andraz213/UrbanNoiseSensing/Diplomska naloga/fotografije/ekran_gateway.jpg

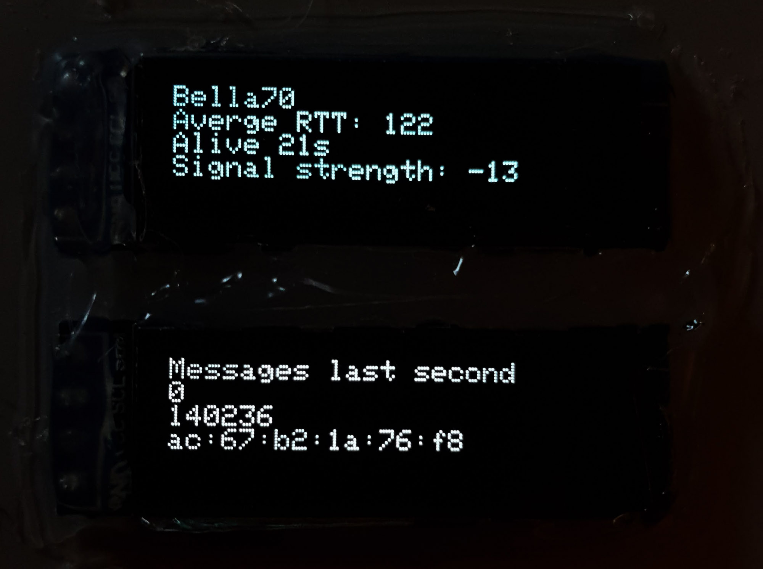
Diplomska naloga/fotografije/ekran_gateway.jpg
