andraz213/UrbanNoiseSensing/Diplomska naloga/fotografije/nastavljanje.jpg

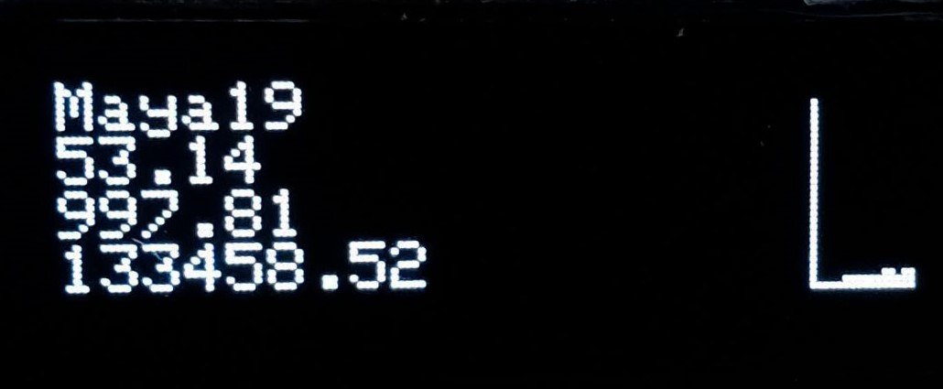
Diplomska naloga/fotografije/nastavljanje.jpg
