andraz213/UrbanNoiseSensing/Diplomska naloga/fotografije/nastavljanje_nastavljenno.jpg

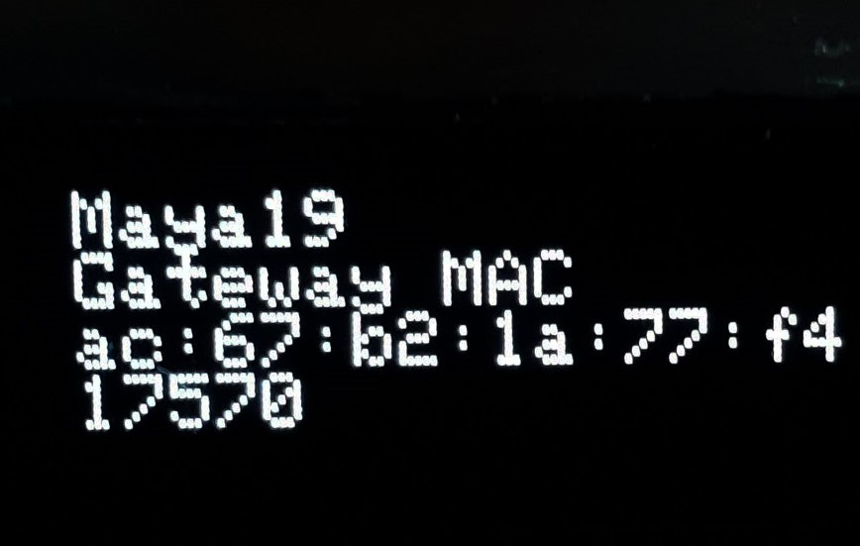
Diplomska naloga/fotografije/nastavljanje_nastavljenno.jpg
