andraz213/UrbanNoiseSensing/Diplomska naloga/fotografije/nastavljeno_nenastavljeno.jpg

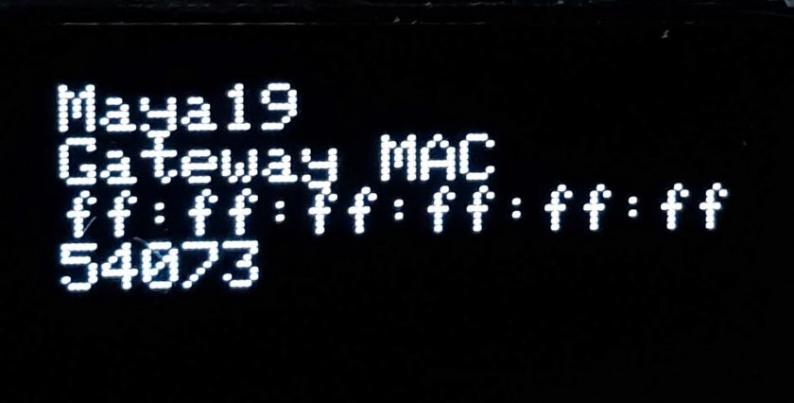
Diplomska naloga/fotografije/nastavljeno_nenastavljeno.jpg
