andraz213/UrbanNoiseSensing/Diplomska naloga/fotografije/polnenje.jpg

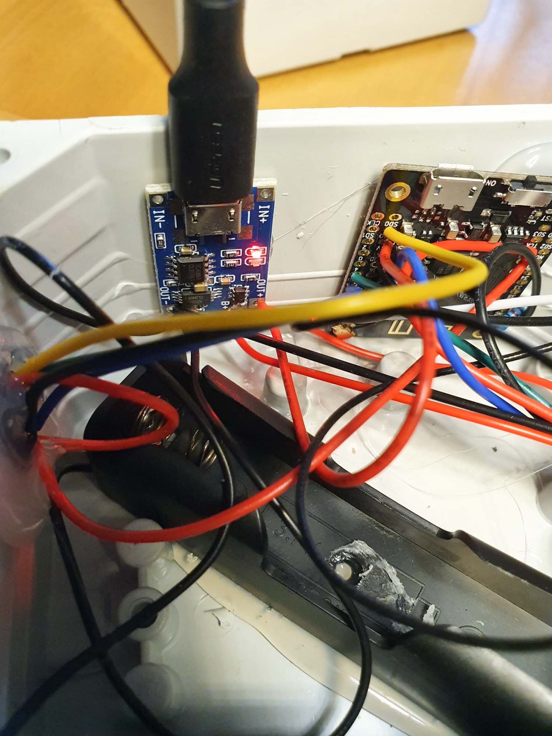
Diplomska naloga/fotografije/polnenje.jpg
