andraz213/UrbanNoiseSensing/Diplomska naloga/fotografije/polnenje_done.jpg

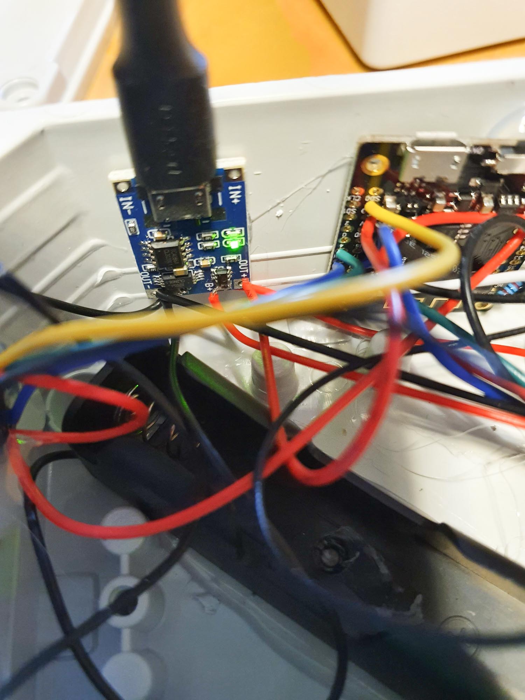
Diplomska naloga/fotografije/polnenje_done.jpg
