andraz213/UrbanNoiseSensing/Diplomska naloga/fotografije/priziganje_zaznavanje.jpg

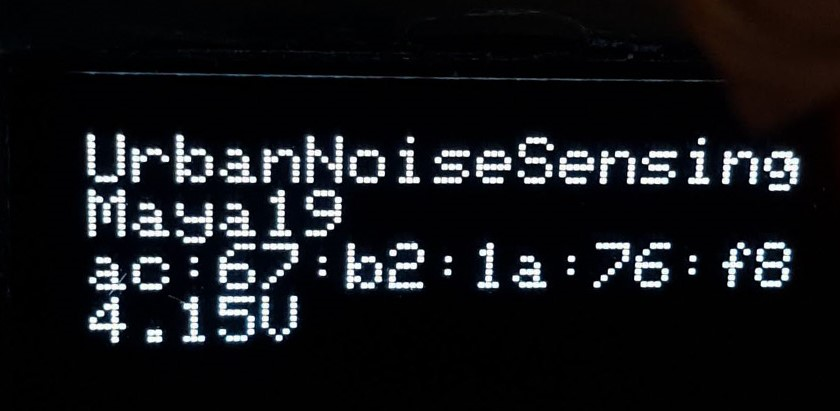
Diplomska naloga/fotografije/priziganje_zaznavanje.jpg
