andraz213/UrbanNoiseSensing/Diplomska naloga/fotografije/sestavljena_merilna1.jpg

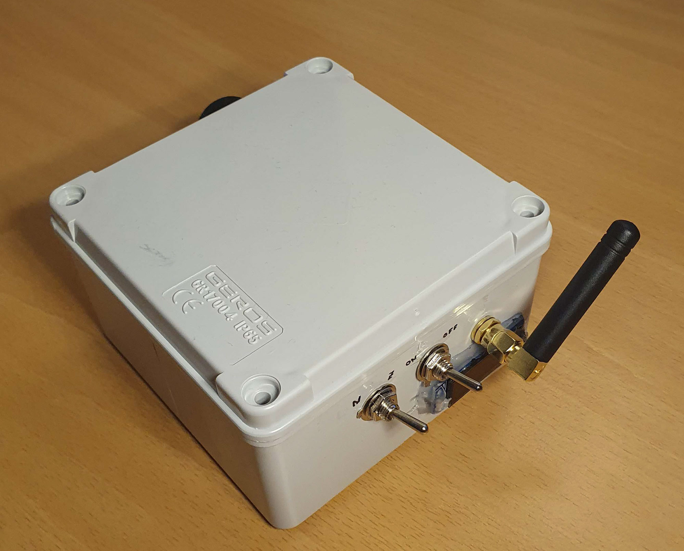
Diplomska naloga/fotografije/sestavljena_merilna1.jpg
