andraz213/UrbanNoiseSensing/Diplomska naloga/fotografije/sestavljena_merilna3.jpg

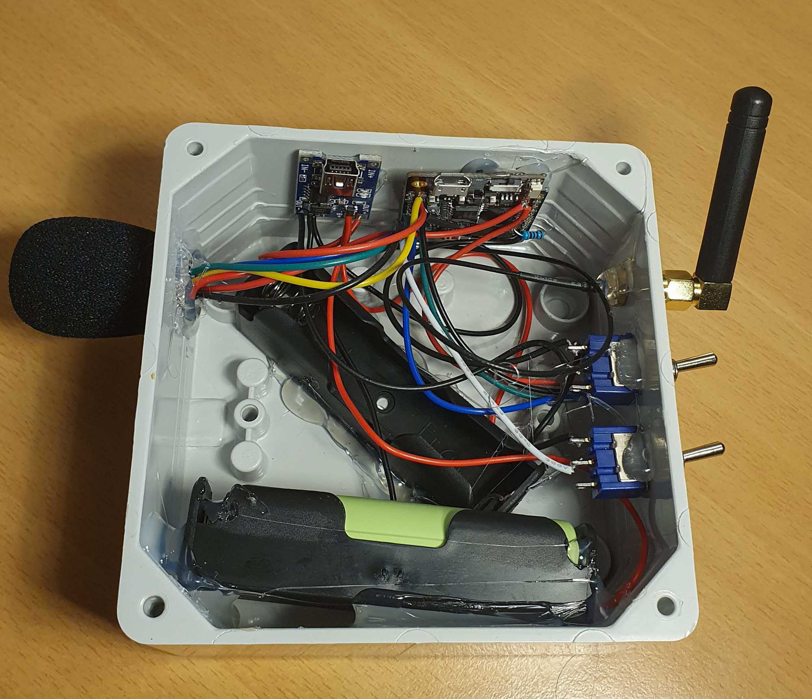
Diplomska naloga/fotografije/sestavljena_merilna3.jpg
