andraz213/UrbanNoiseSensing/Diplomska naloga/fotografije/sestavljena_zbirna1.jpg

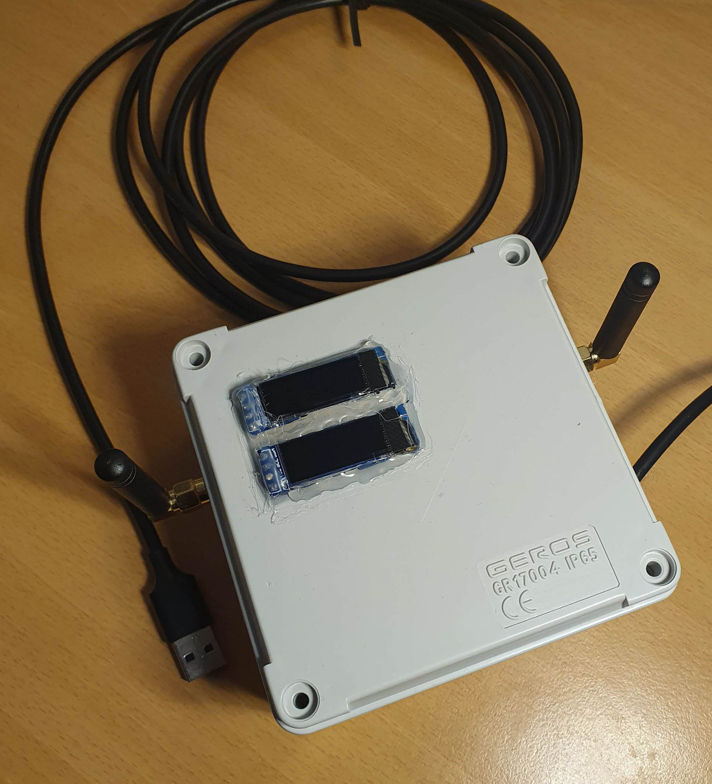
Diplomska naloga/fotografije/sestavljena_zbirna1.jpg
