andraz213/UrbanNoiseSensing/Diplomska naloga/fotografije/sestavljena_zbirna2.jpg

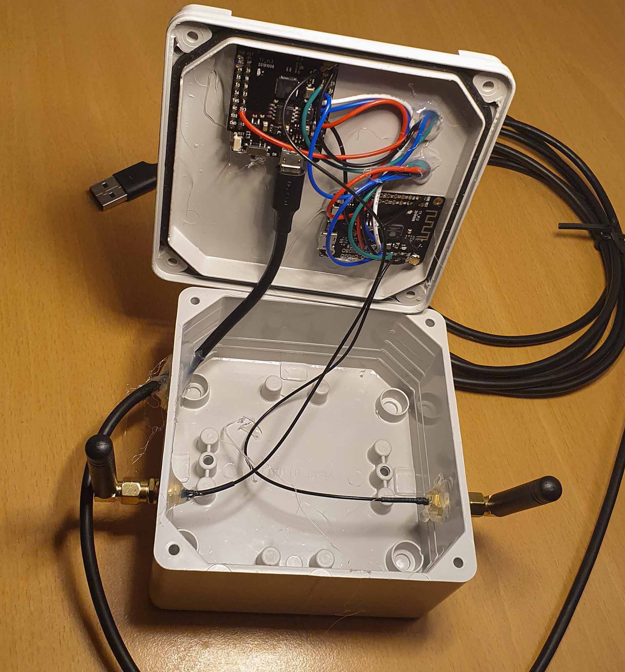
Diplomska naloga/fotografije/sestavljena_zbirna2.jpg
