andraz213/UrbanNoiseSensing/Diplomska naloga/fotografije/stikala.jpg

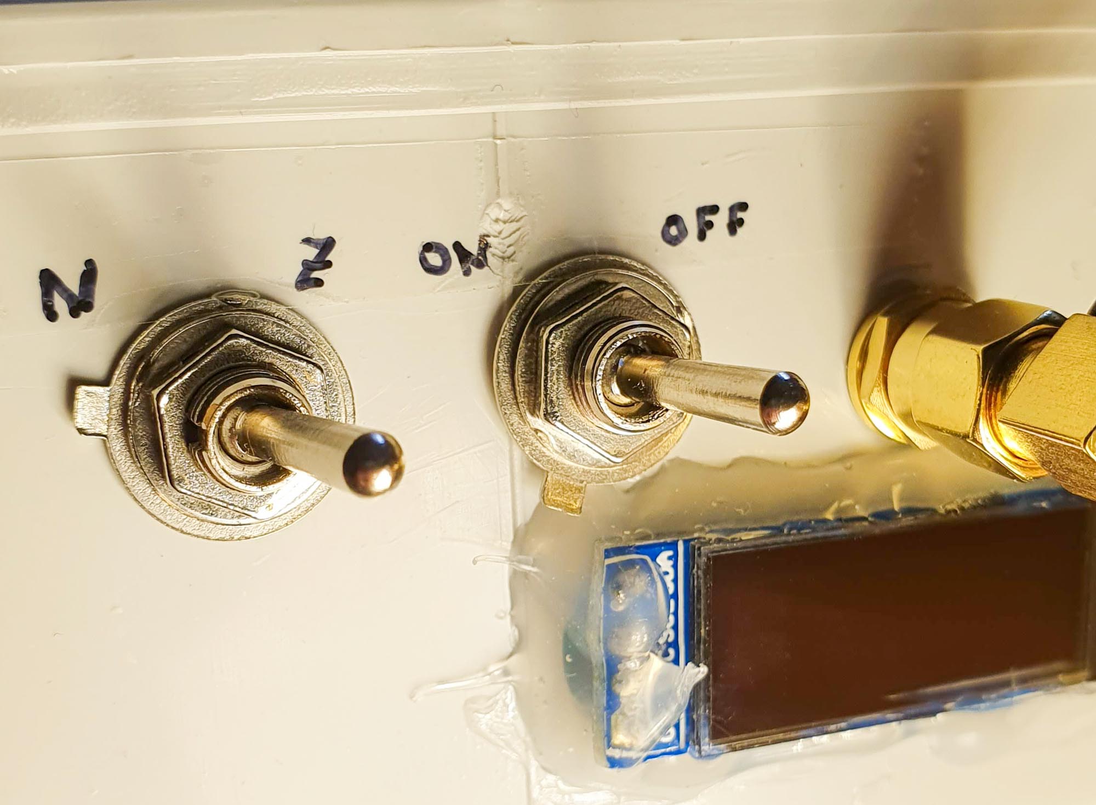
Diplomska naloga/fotografije/stikala.jpg
