andraz213/UrbanNoiseSensing/Diplomska naloga/slike/data_matrica.png

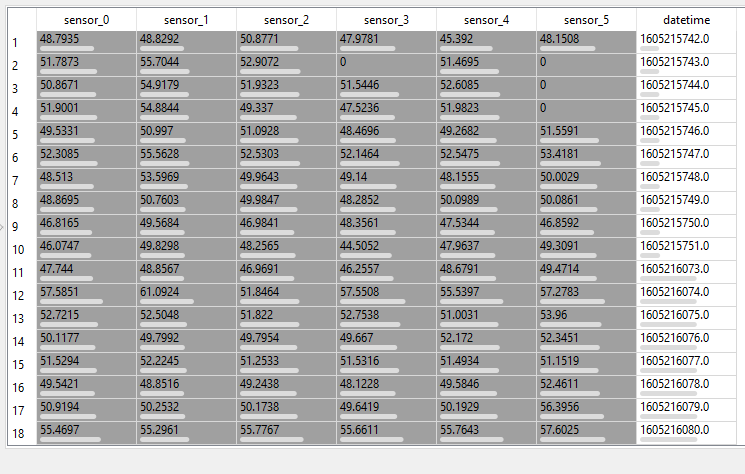
Diplomska naloga/slike/data_matrica.png
