andraz213/UrbanNoiseSensing/Diplomska naloga/slike/data_tenzorji.png

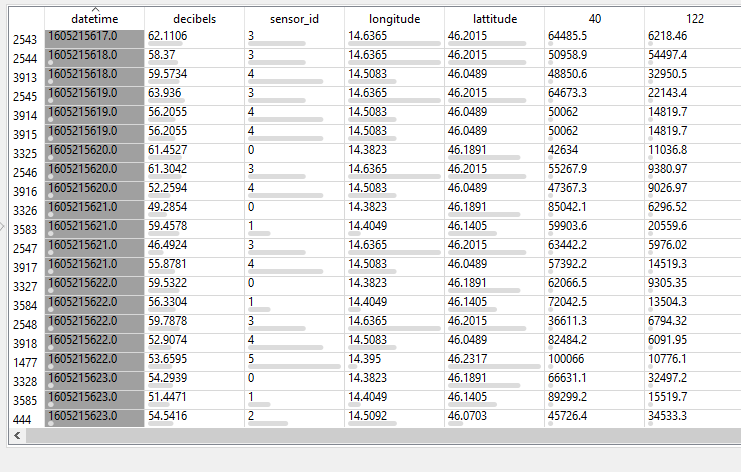
Diplomska naloga/slike/data_tenzorji.png
