andraz213/UrbanNoiseSensing/Diplomska naloga/slike/db_data.jpg

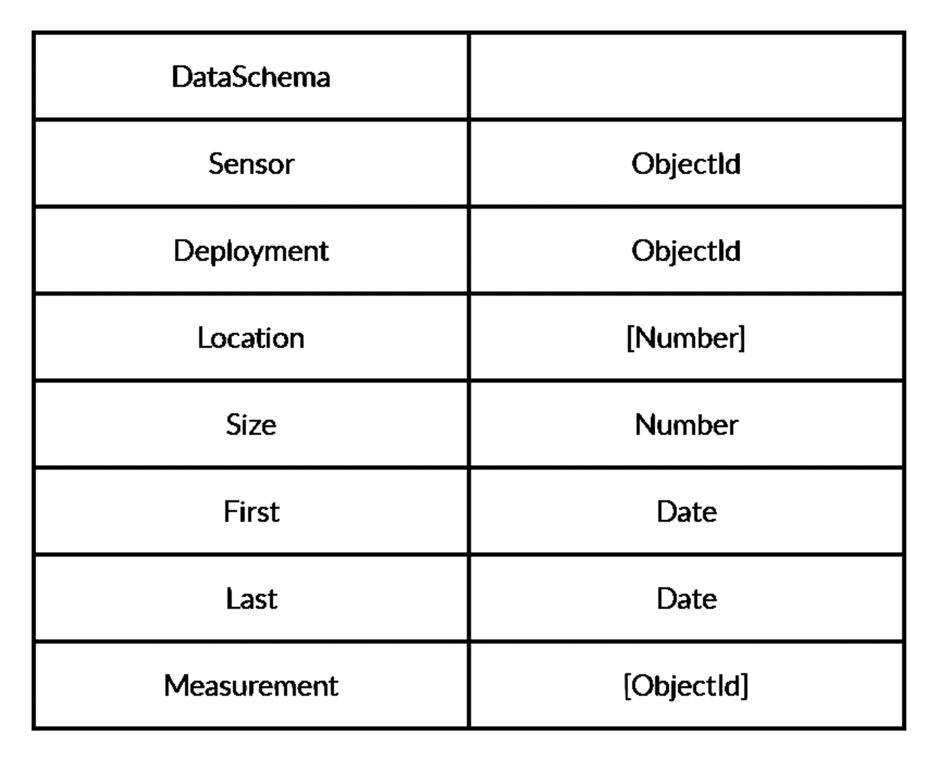
Diplomska naloga/slike/db_data.jpg
