andraz213/UrbanNoiseSensing/Diplomska naloga/slike/db_deployment.jpg

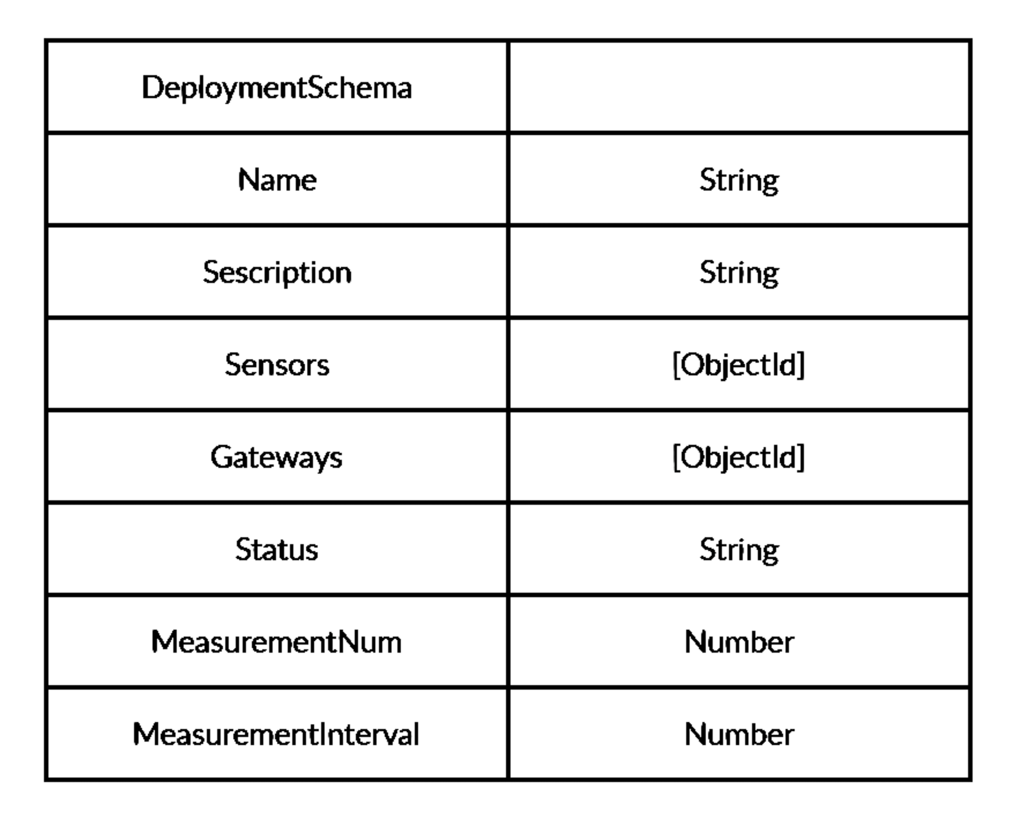
Diplomska naloga/slike/db_deployment.jpg
