andraz213/UrbanNoiseSensing/Diplomska naloga/slike/db_merilna_zbirna.jpg

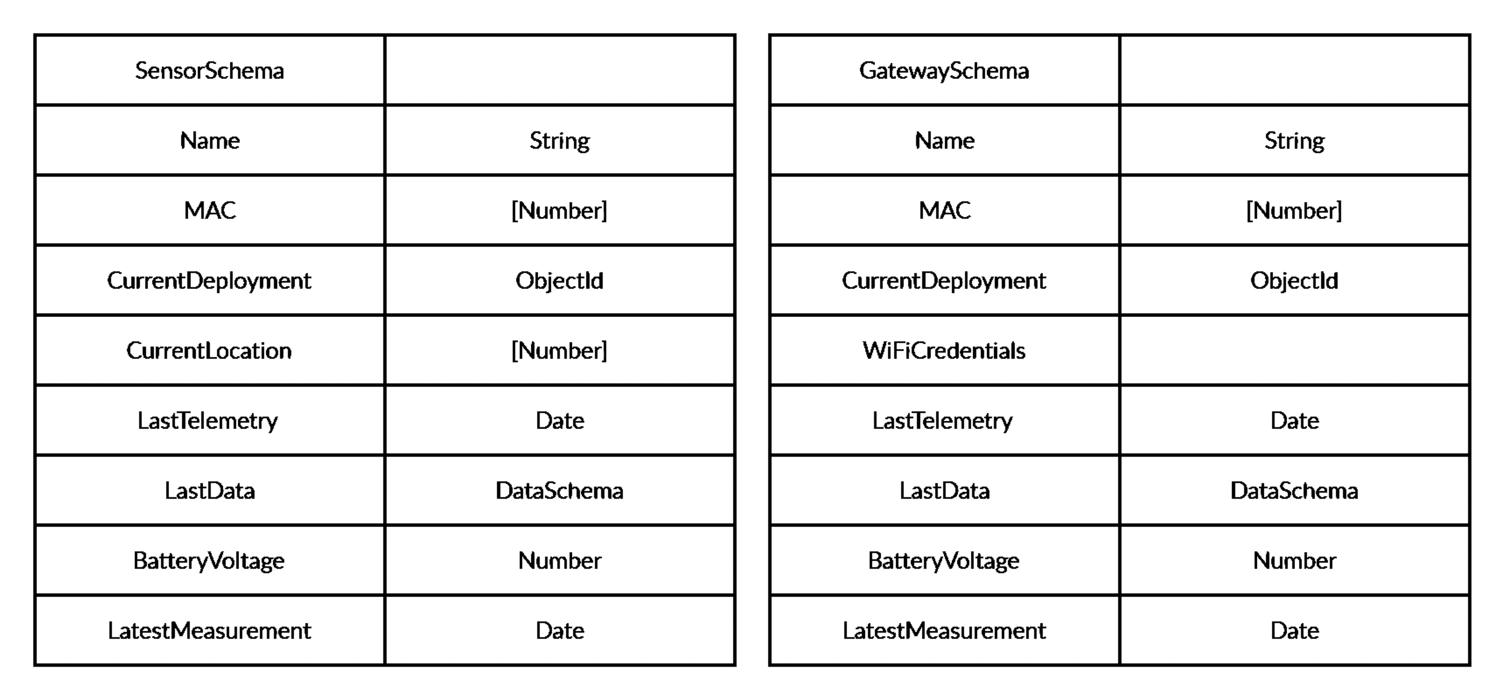
Diplomska naloga/slike/db_merilna_zbirna.jpg
