andraz213/UrbanNoiseSensing/Diplomska naloga/slike/Detajli poraba.png

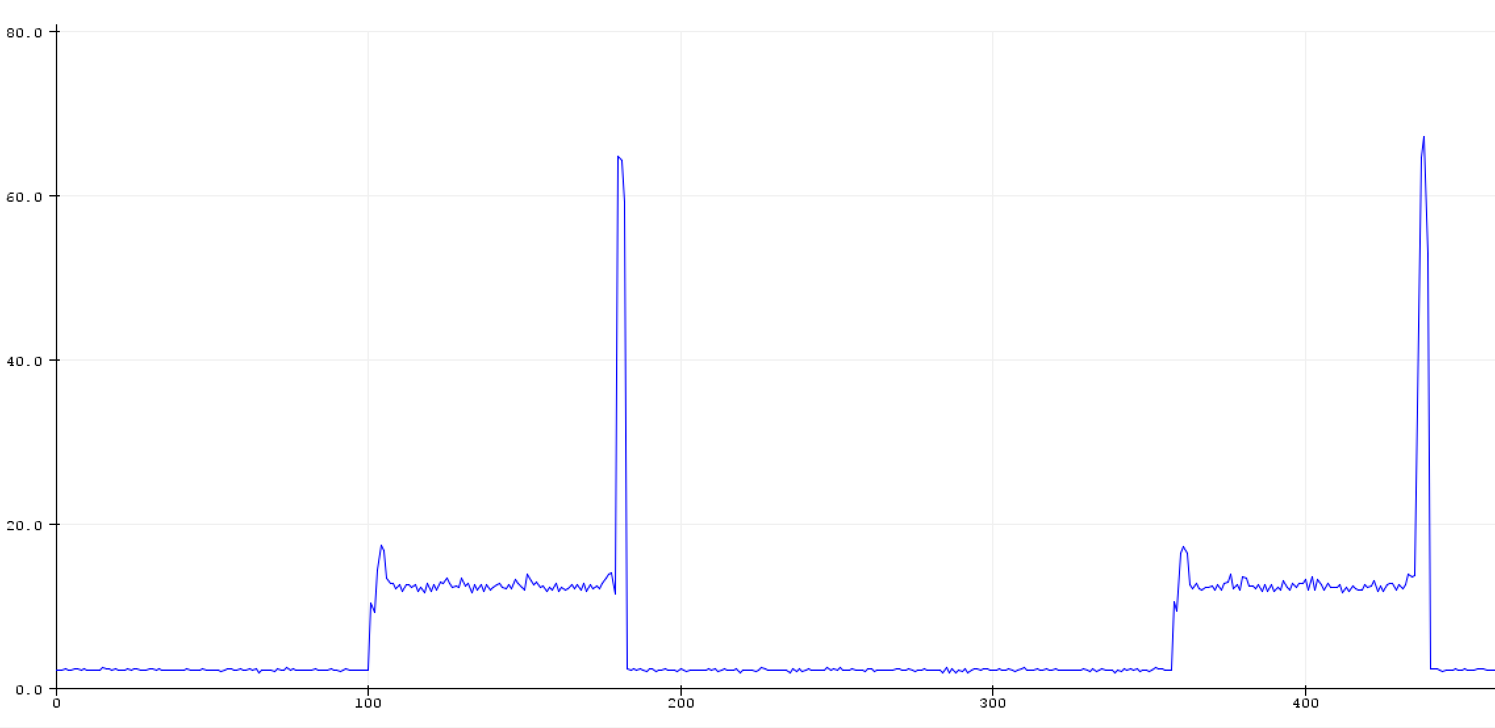
Diplomska naloga/slike/Detajli poraba.png
