andraz213/UrbanNoiseSensing/Diplomska naloga/slike/graf_dnevi_dnevna.png

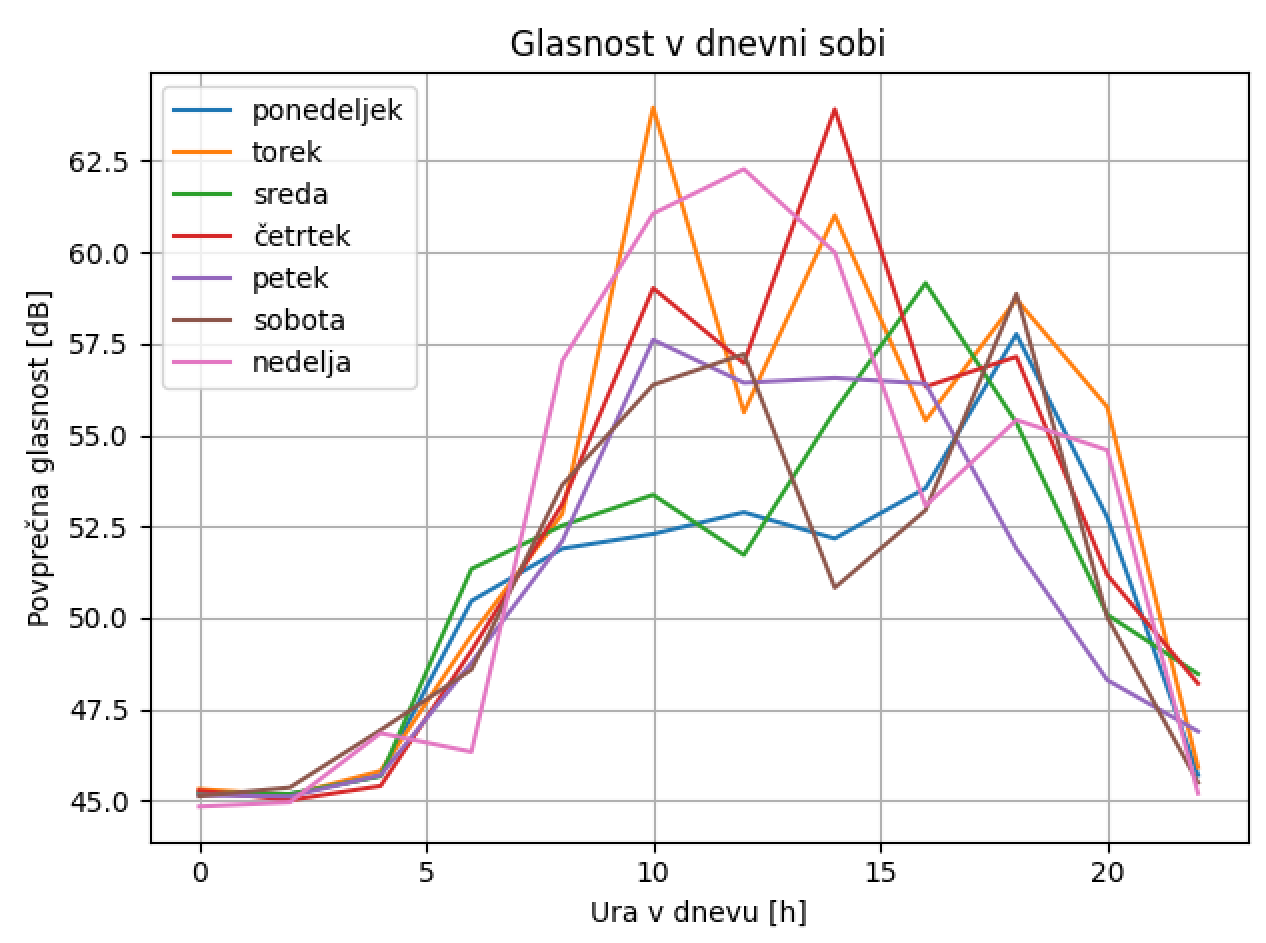
Diplomska naloga/slike/graf_dnevi_dnevna.png
