andraz213/UrbanNoiseSensing/Diplomska naloga/slike/graf_dnevna.png

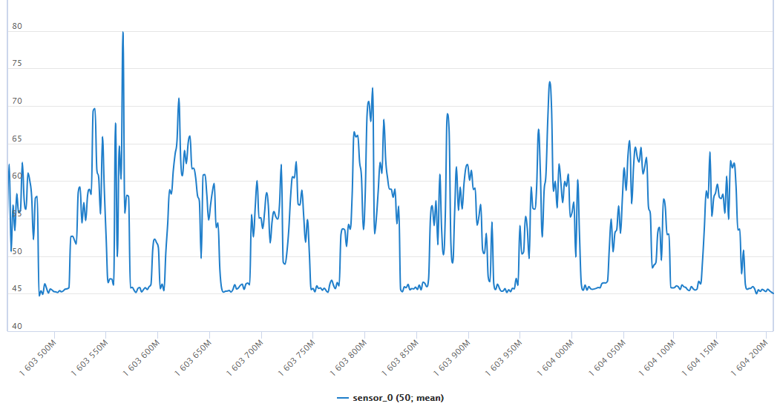
Diplomska naloga/slike/graf_dnevna.png
