andraz213/UrbanNoiseSensing/Diplomska naloga/slike/Konceptualna shema merilne enote (2)_popravljeno.jpg

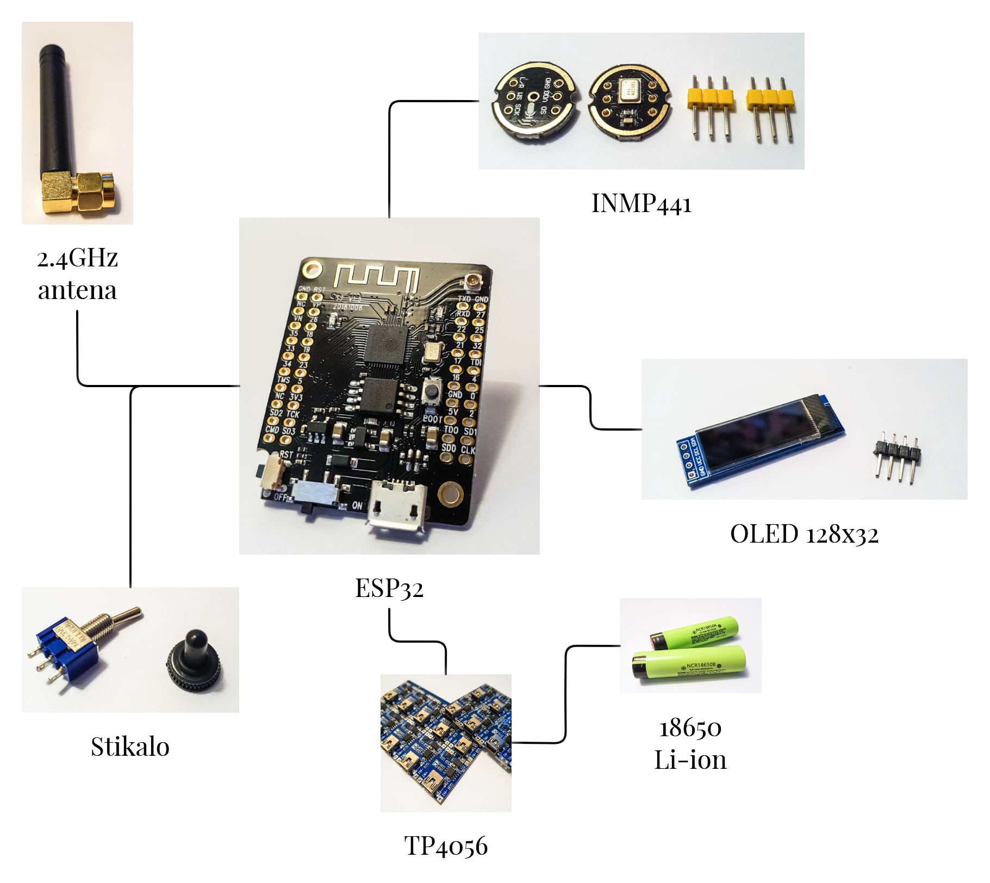
Diplomska naloga/slike/Konceptualna shema merilne enote (2)_popravljeno.jpg
