andraz213/UrbanNoiseSensing/Diplomska naloga/slike/kosilnica mapa 2.png

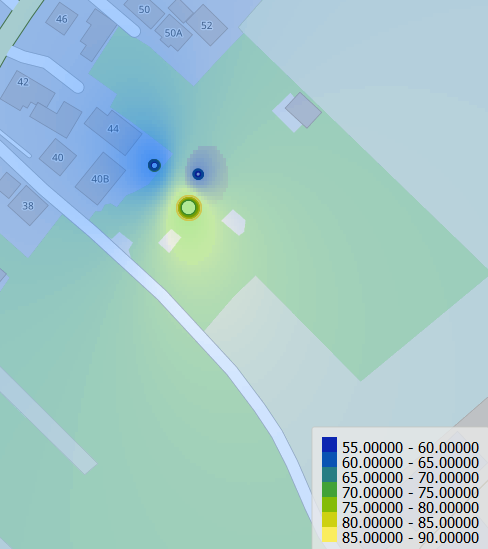
Diplomska naloga/slike/kosilnica mapa 2.png
