andraz213/UrbanNoiseSensing/Diplomska naloga/slike/Kosilnica mapa.png

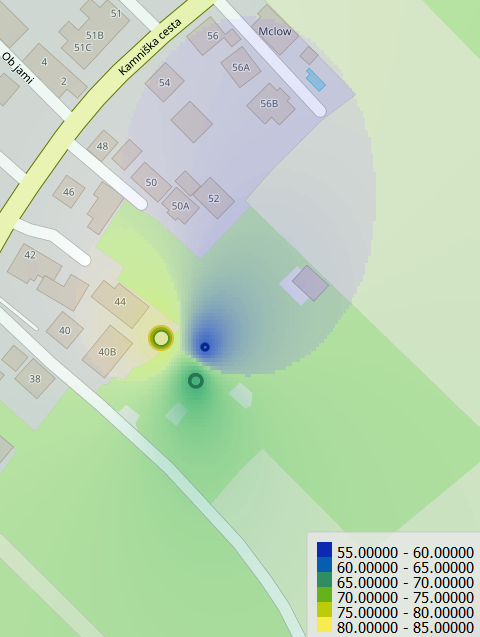
Diplomska naloga/slike/Kosilnica mapa.png
