andraz213/UrbanNoiseSensing/Diplomska naloga/slike/kosilnica_graf.png

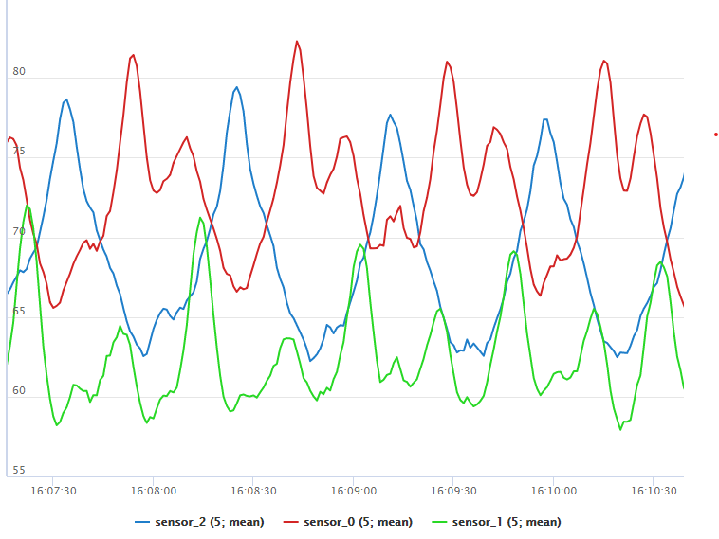
Diplomska naloga/slike/kosilnica_graf.png
