andraz213/UrbanNoiseSensing/Diplomska naloga/slike/Libellium_enote.png

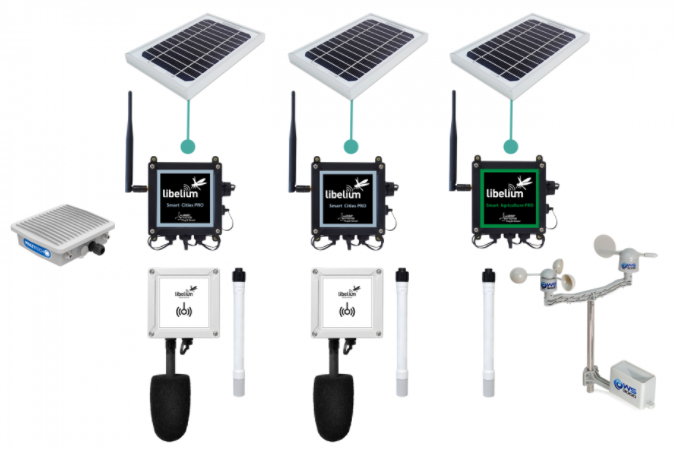
Diplomska naloga/slike/Libellium_enote.png
