andraz213/UrbanNoiseSensing/Diplomska naloga/slike/Merilna enota delovanje (1)_popravljeno.jpg

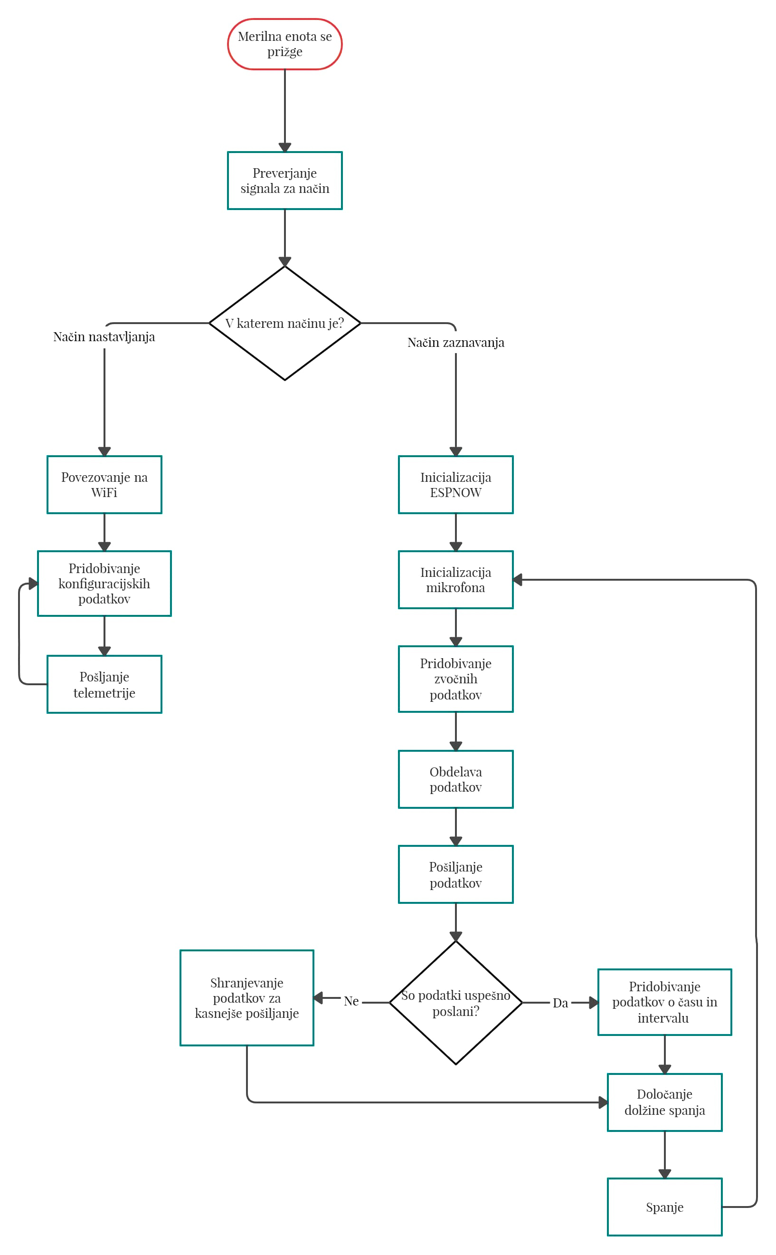
Diplomska naloga/slike/Merilna enota delovanje (1)_popravljeno.jpg
