andraz213/UrbanNoiseSensing/Diplomska naloga/slike/Normalna poraba na eno sekundo.png

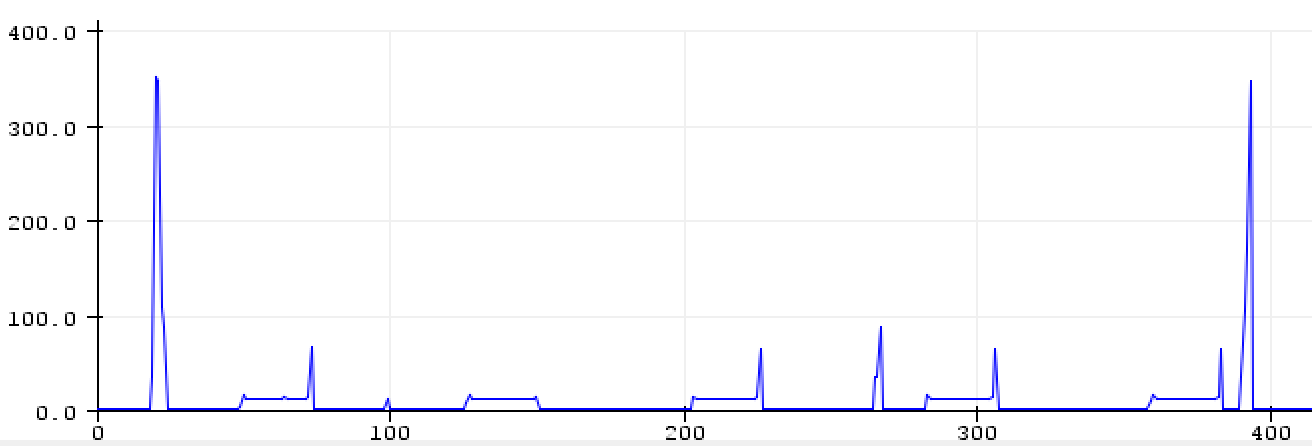
Diplomska naloga/slike/Normalna poraba na eno sekundo.png
