andraz213/UrbanNoiseSensing/Diplomska naloga/slike/periodogram_dnnevna.png

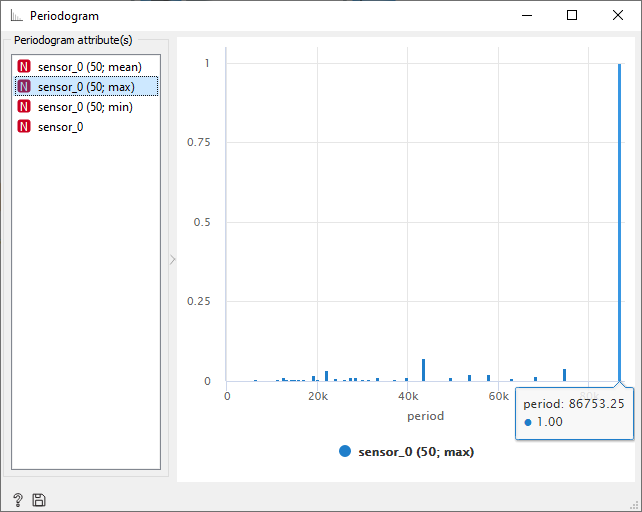
Diplomska naloga/slike/periodogram_dnnevna.png
