andraz213/UrbanNoiseSensing/Diplomska naloga/slike/podoben_mojemu.png

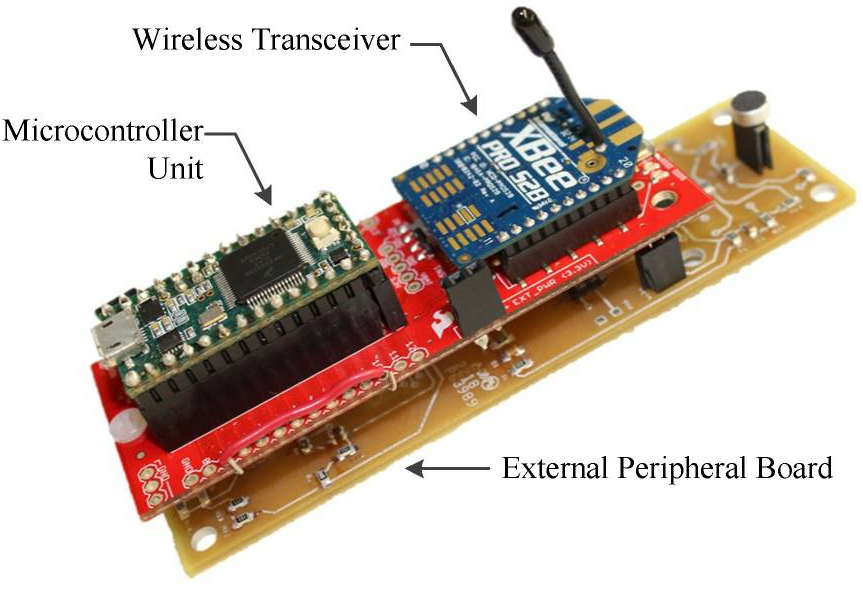
Diplomska naloga/slike/podoben_mojemu.png
