andraz213/UrbanNoiseSensing/Diplomska naloga/slike/poraba_detaili_fakpng.png

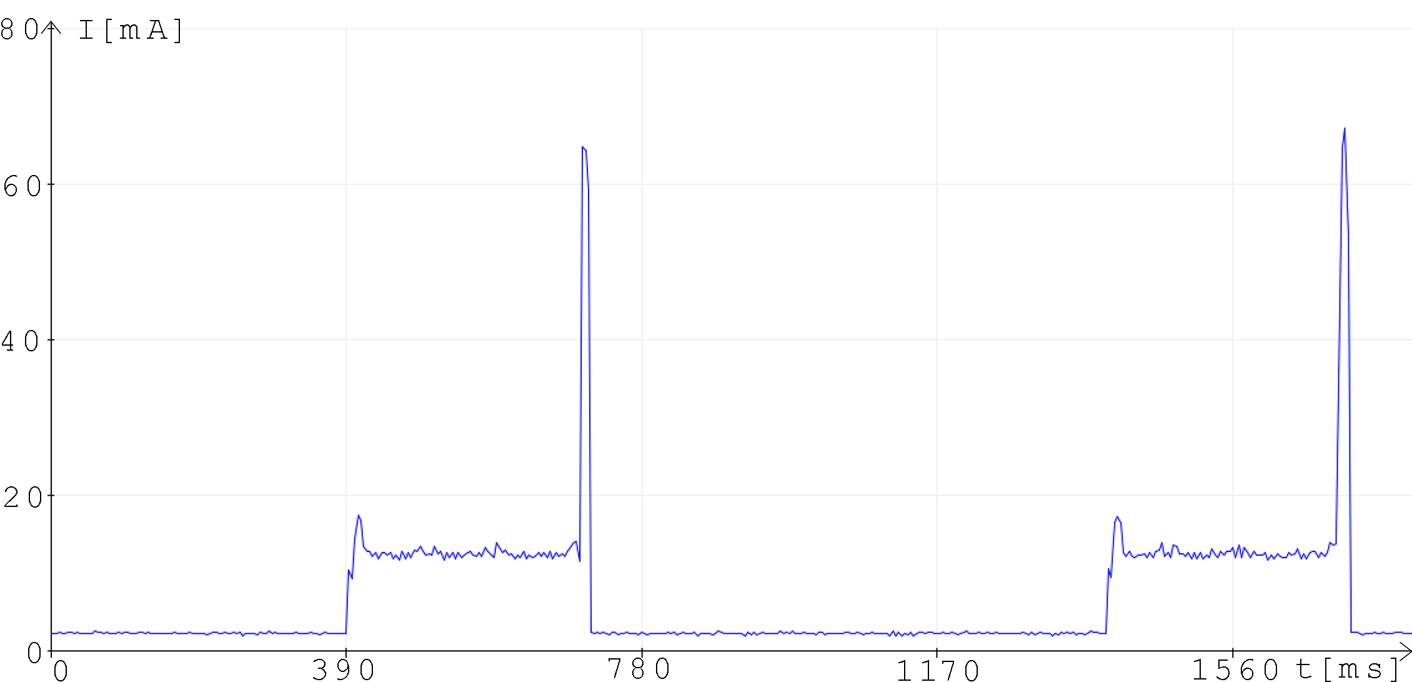
Diplomska naloga/slike/poraba_detaili_fakpng.png
