andraz213/UrbanNoiseSensing/Diplomska naloga/slike/postavljene_merilne_enote.png

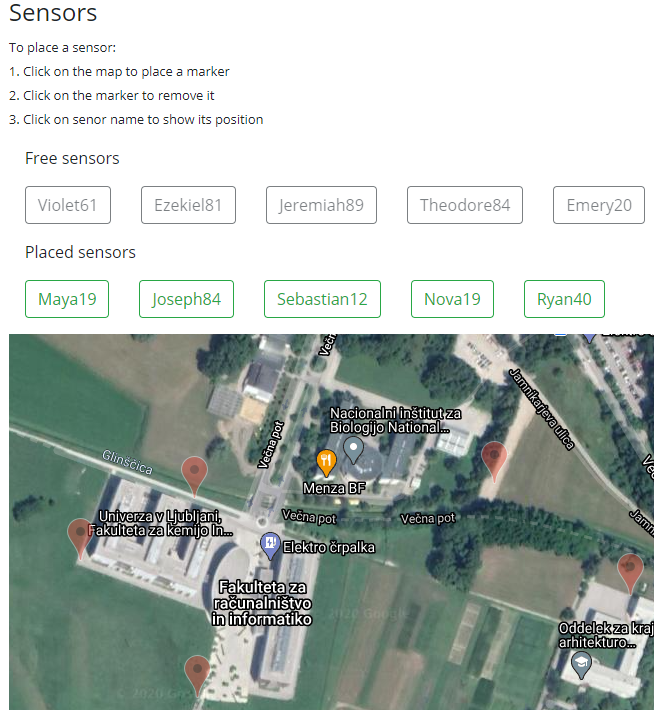
Diplomska naloga/slike/postavljene_merilne_enote.png
