andraz213/UrbanNoiseSensing/Diplomska naloga/slike/Primer uporabe.png

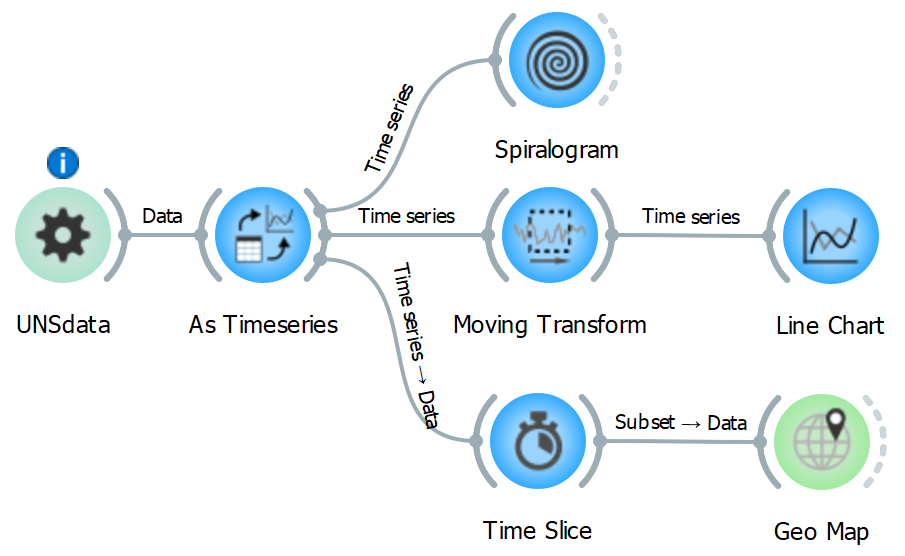
Diplomska naloga/slike/Primer uporabe.png
