andraz213/UrbanNoiseSensing/Diplomska naloga/slike/Shema celote arhitekture (2)_popravljeno.jpg

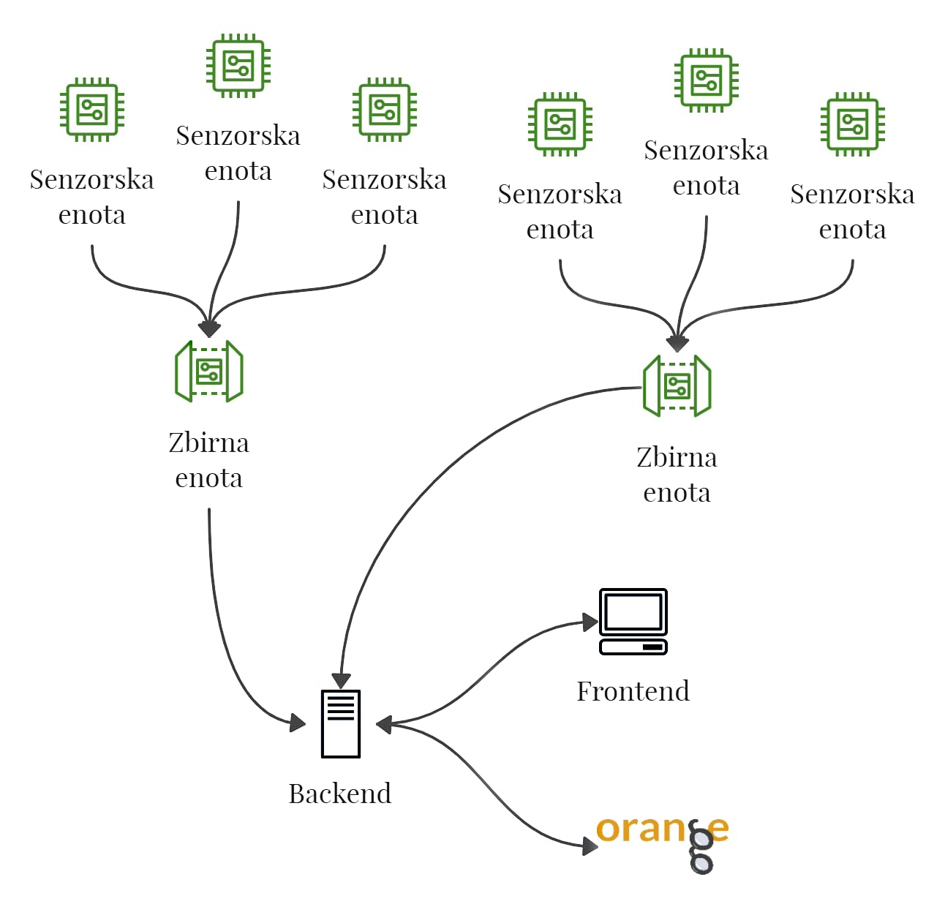
Diplomska naloga/slike/Shema celote arhitekture (2)_popravljeno.jpg
