andraz213/UrbanNoiseSensing/Diplomska naloga/slike/Shema celote arhitekture (3)_popravljeno.jpg

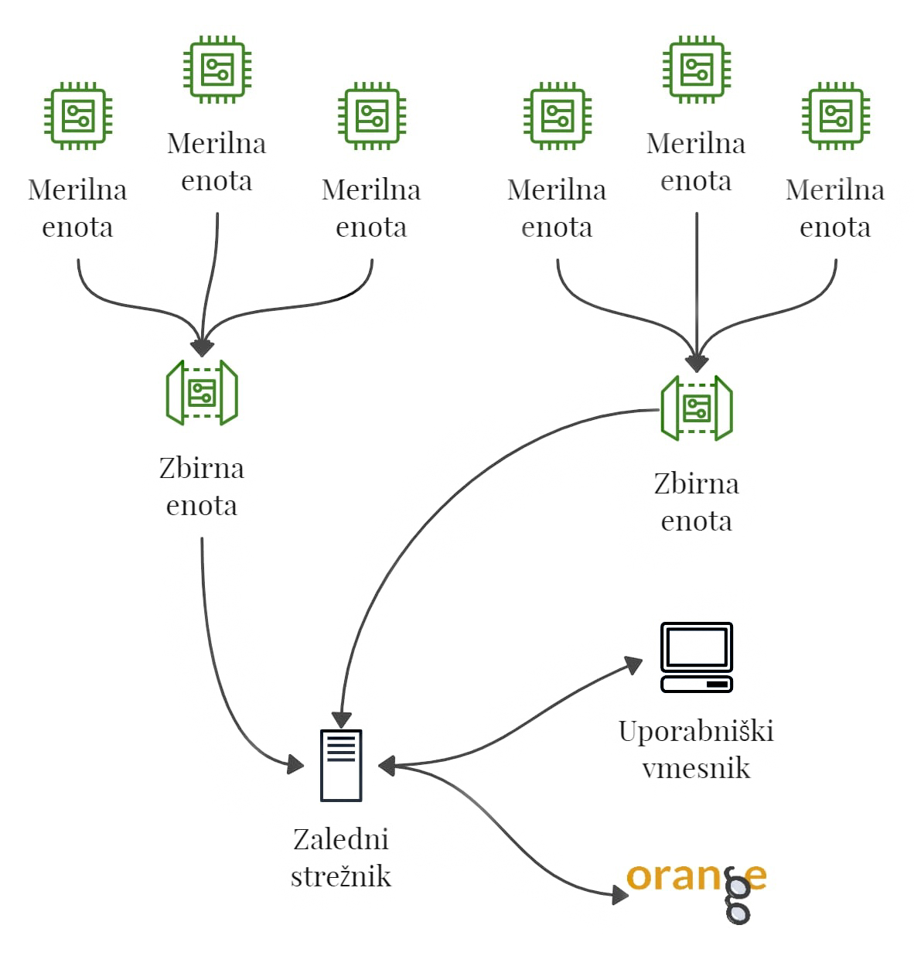
Diplomska naloga/slike/Shema celote arhitekture (3)_popravljeno.jpg
