andraz213/UrbanNoiseSensing/Diplomska naloga/slike/UNSdata_widget.png

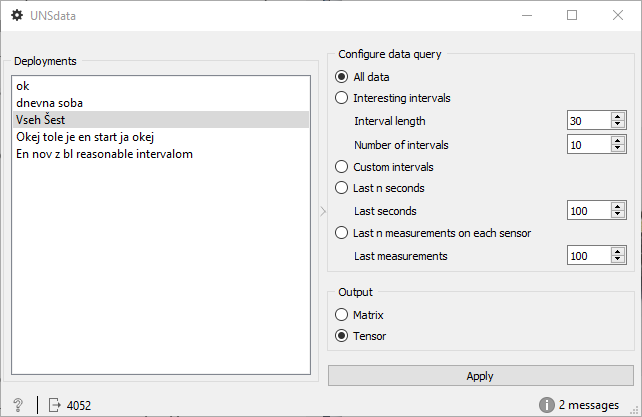
Diplomska naloga/slike/UNSdata_widget.png
