andraz213/UrbanNoiseSensing/Diplomska naloga/slike/uv-deployments-pregled.png

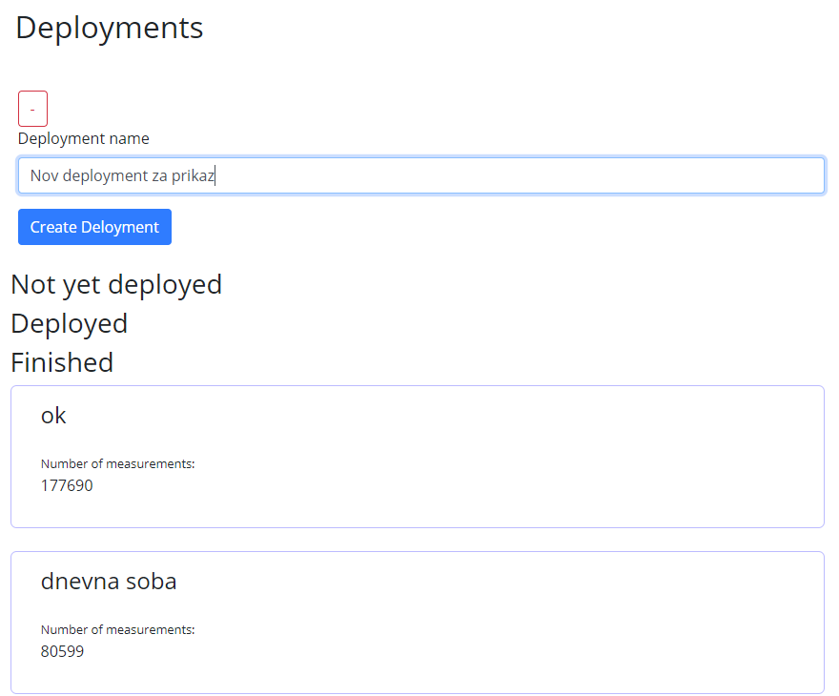
Diplomska naloga/slike/uv-deployments-pregled.png
