andraz213/UrbanNoiseSensing/Diplomska naloga/slike/uv-graf.png

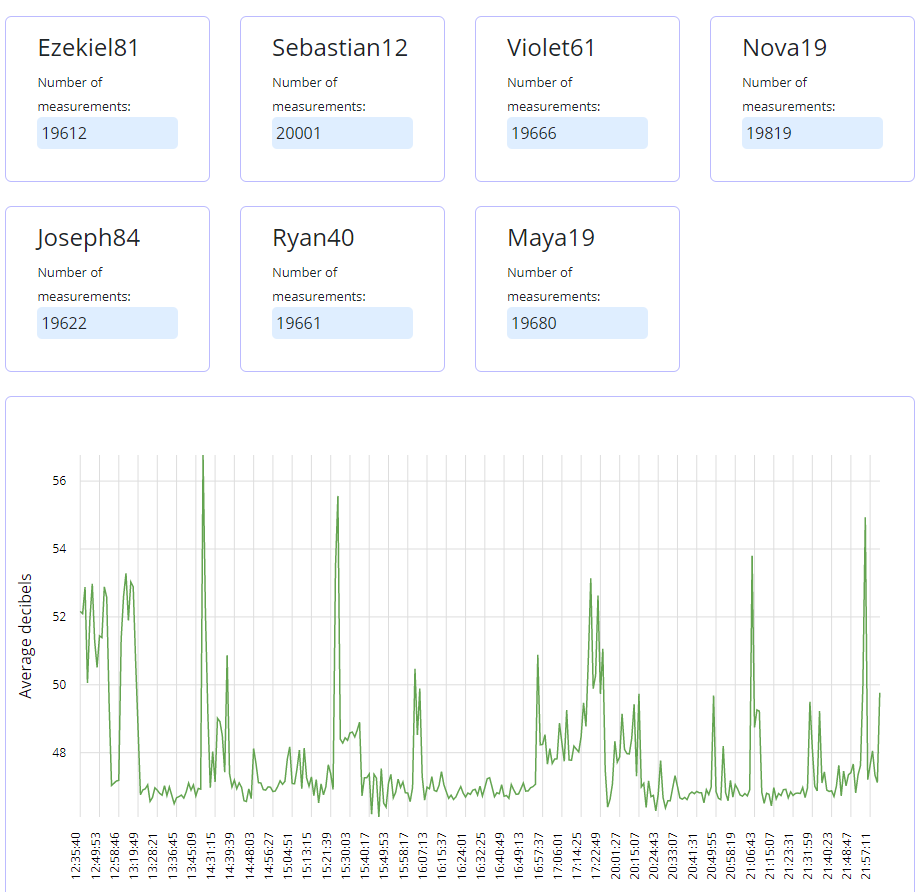
Diplomska naloga/slike/uv-graf.png
