andraz213/UrbanNoiseSensing/Diplomska naloga/slike/uv-merilne-enote.png

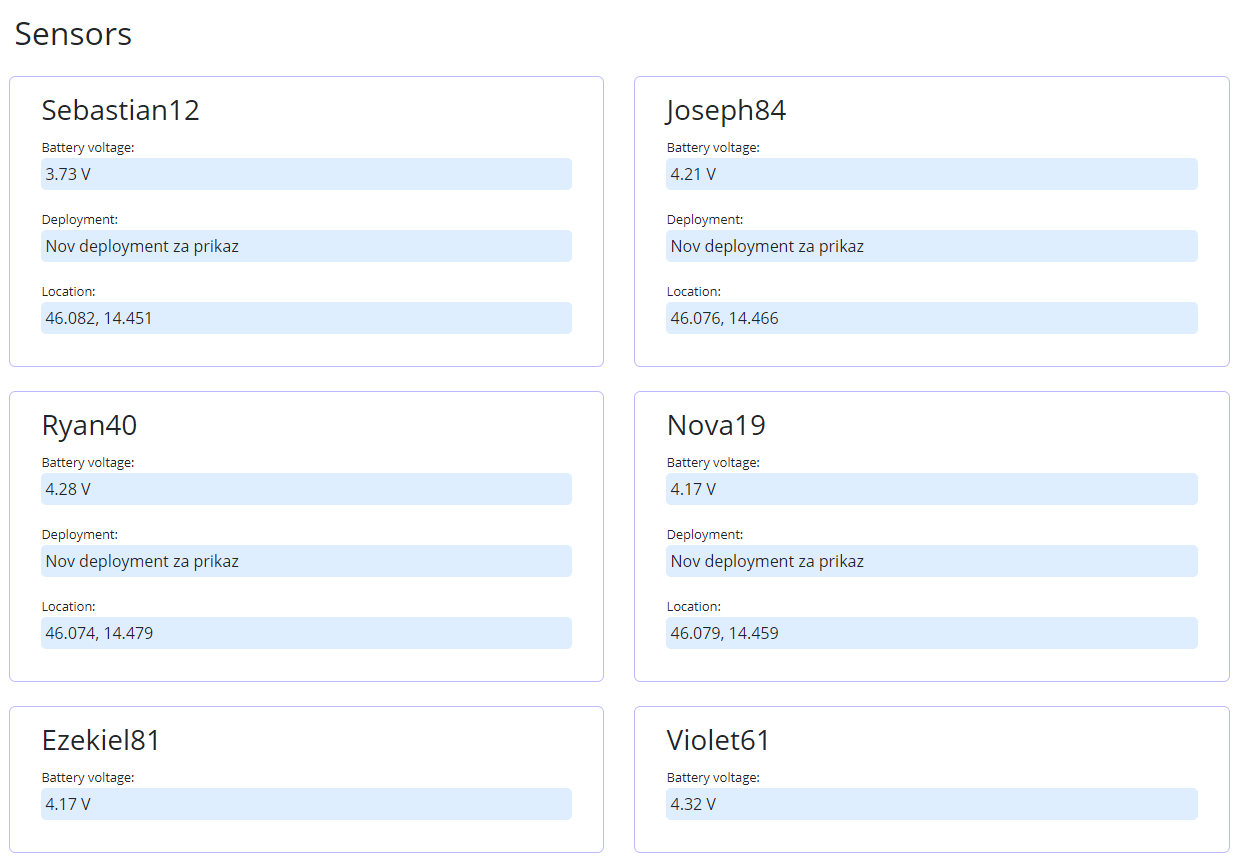
Diplomska naloga/slike/uv-merilne-enote.png
