andraz213/UrbanNoiseSensing/Diplomska naloga/slike/uv-nastavljanje-dep1.png

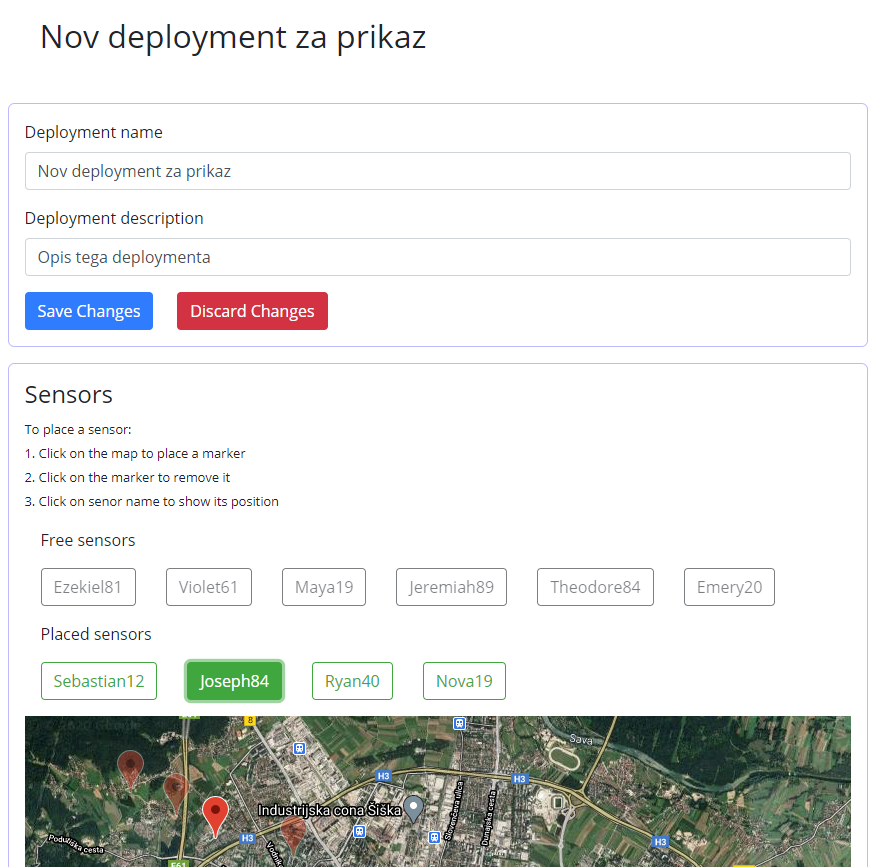
Diplomska naloga/slike/uv-nastavljanje-dep1.png
