andraz213/UrbanNoiseSensing/Diplomska naloga/slike/uv-nastavljanje-gatewayejs.png

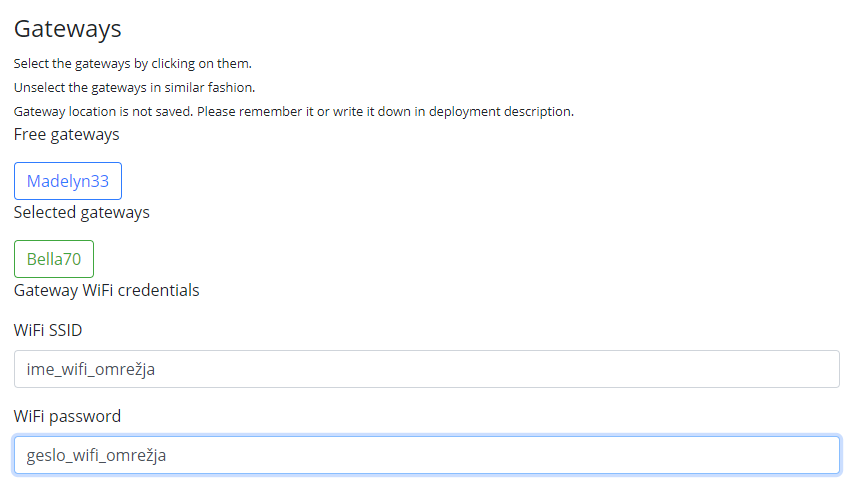
Diplomska naloga/slike/uv-nastavljanje-gatewayejs.png
