andraz213/UrbanNoiseSensing/Diplomska naloga/slike/uv-nastavljanje-zemljevid.png

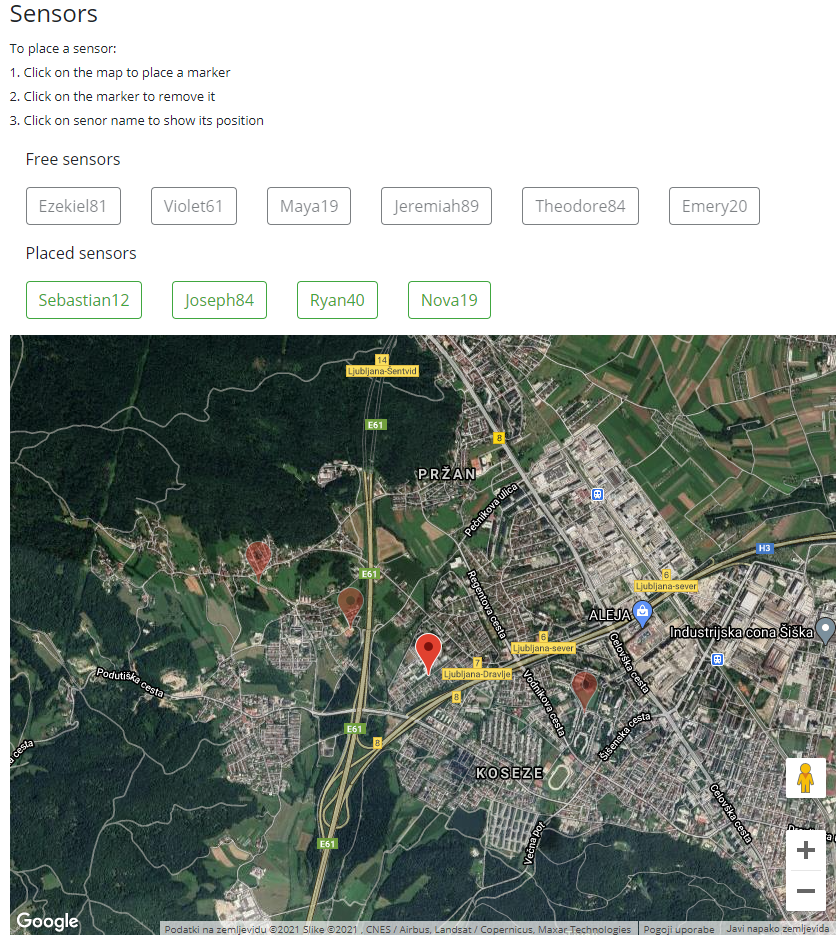
Diplomska naloga/slike/uv-nastavljanje-zemljevid.png
