andraz213/UrbanNoiseSensing/Diplomska naloga/slike/uv-pregled-med-zaznavanjem.png

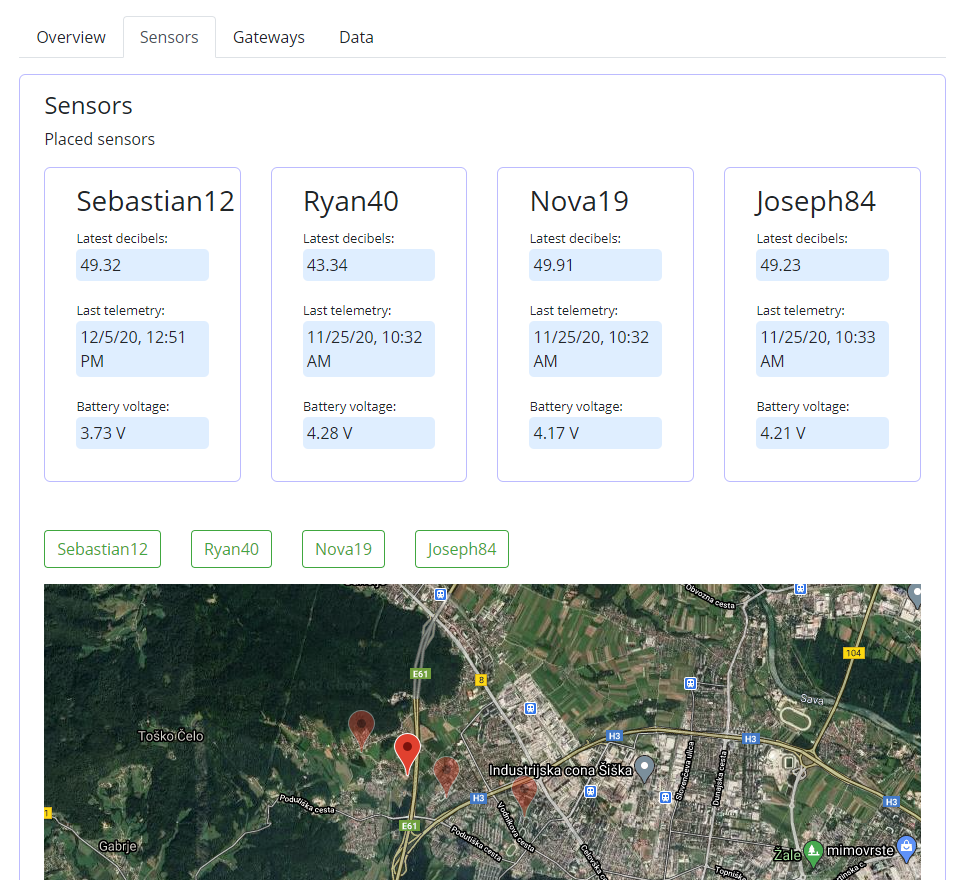
Diplomska naloga/slike/uv-pregled-med-zaznavanjem.png
