andraz213/UrbanNoiseSensing/Diplomska naloga/slike/uv-pregled.png

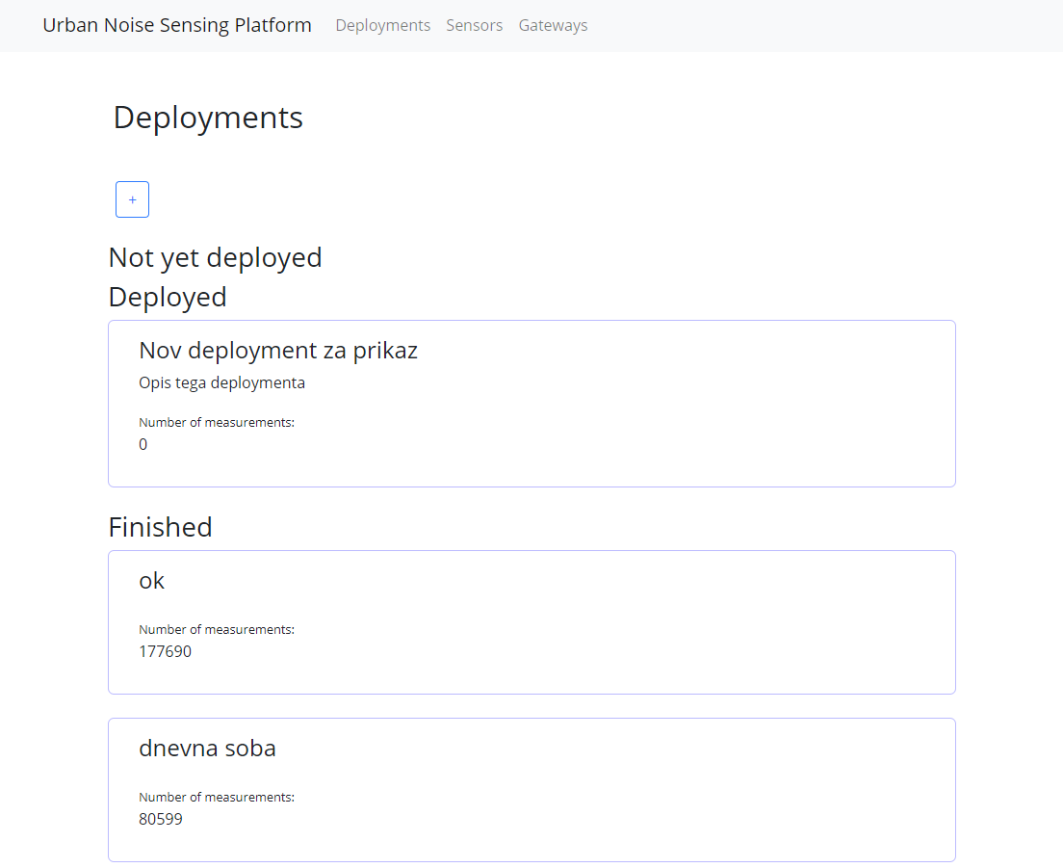
Diplomska naloga/slike/uv-pregled.png
