andraz213/UrbanNoiseSensing/Diplomska naloga/slike/vec_sekund_kurba.png

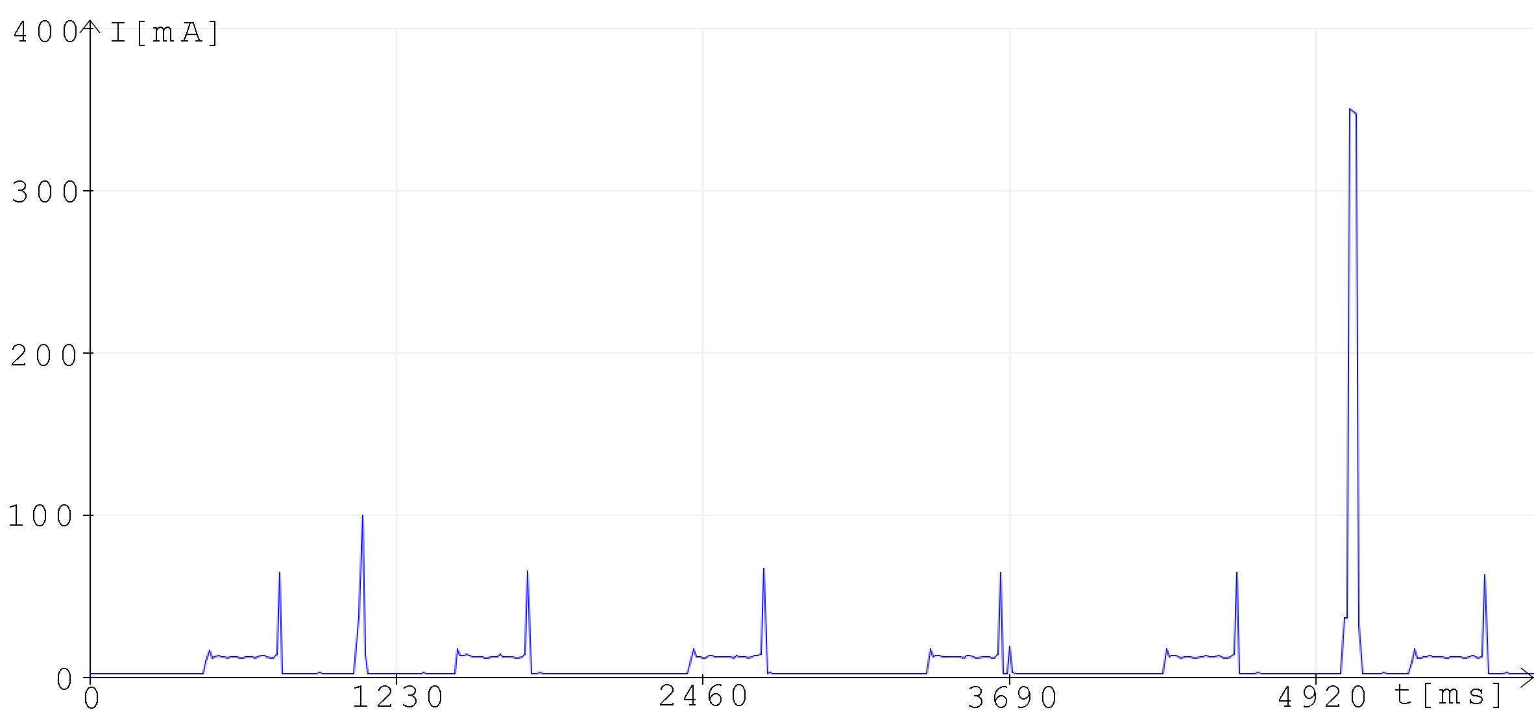
Diplomska naloga/slike/vec_sekund_kurba.png
