andraz213/UrbanNoiseSensing/Diplomska naloga/slike/več sekund poraba.png

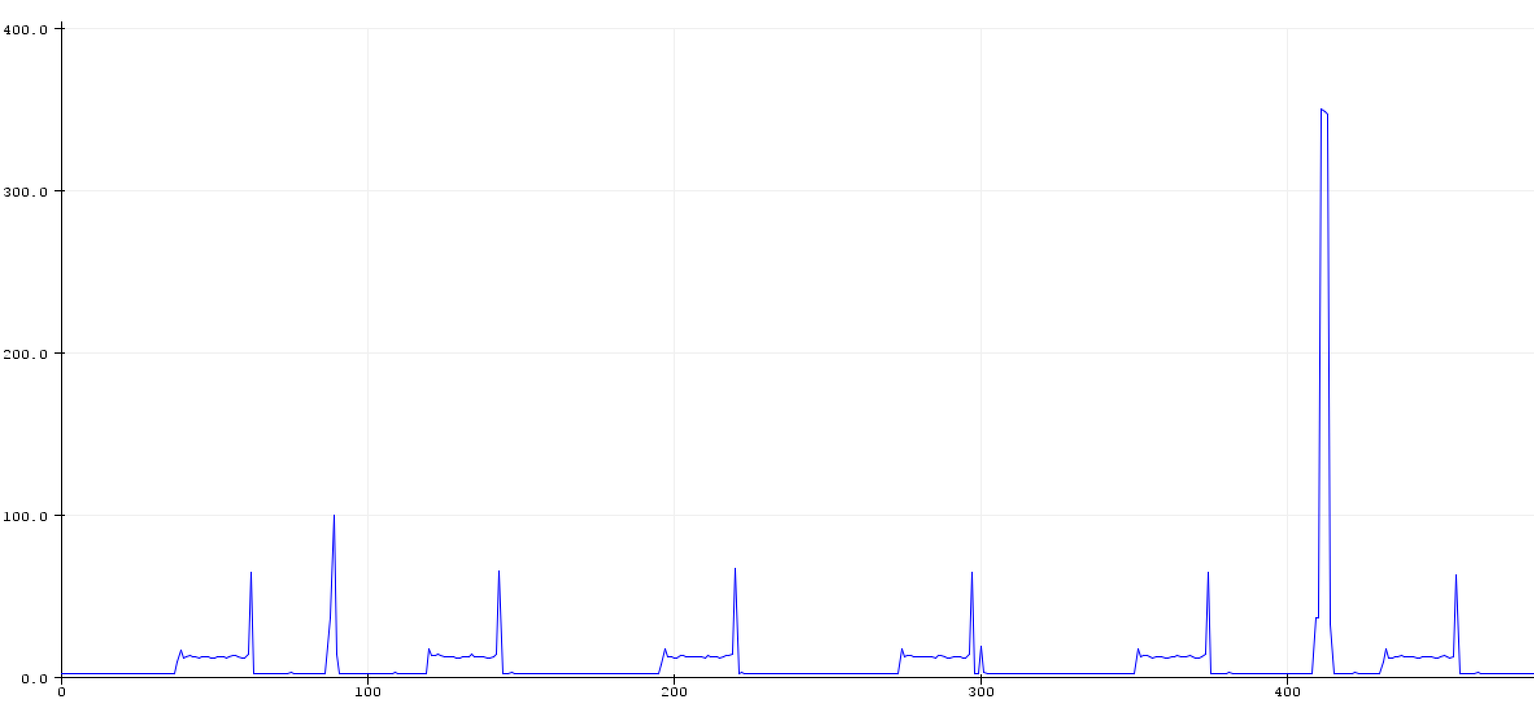
Diplomska naloga/slike/več sekund poraba.png
