andraz213/UrbanNoiseSensing/Diplomska naloga/slike/wf_spiralogram.png

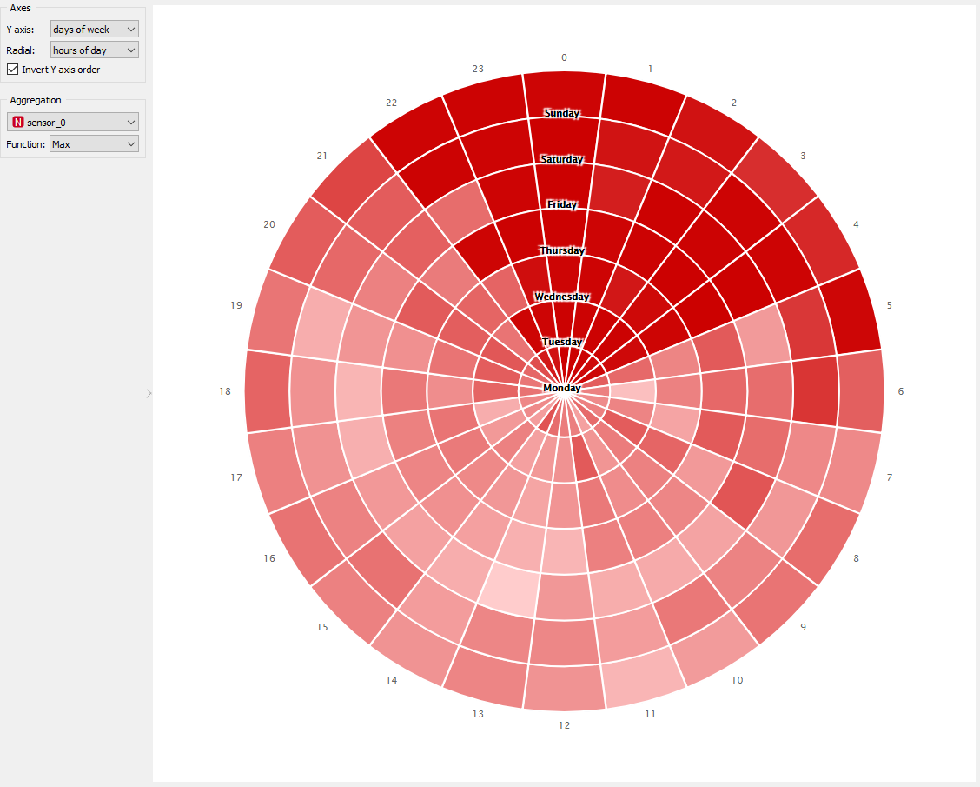
Diplomska naloga/slike/wf_spiralogram.png
