andraz213/UrbanNoiseSensing/Diplomska naloga/slike/workflow kosilnica.png

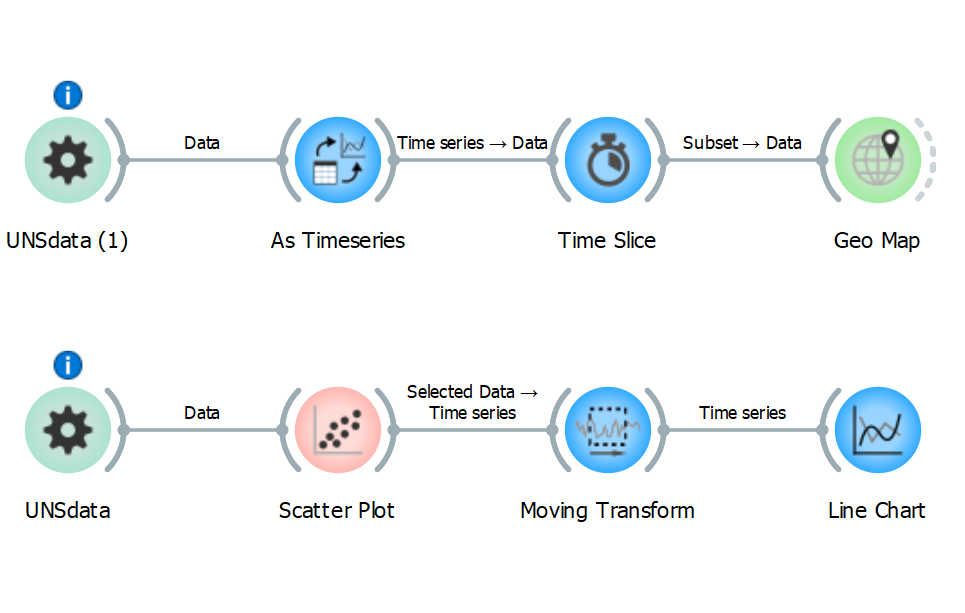
Diplomska naloga/slike/workflow kosilnica.png
