andraz213/UrbanNoiseSensing/Diplomska naloga/slike/workflow_dnnevna.png

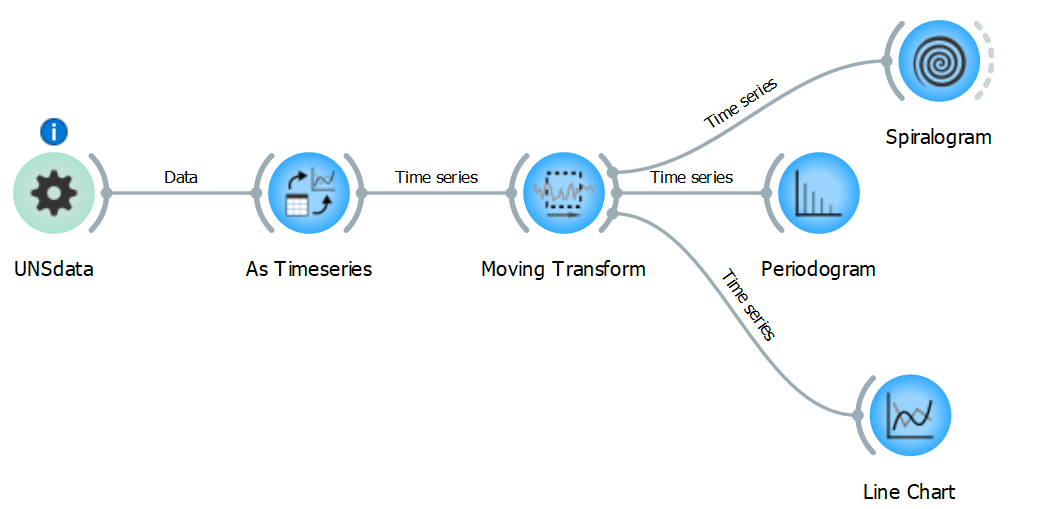
Diplomska naloga/slike/workflow_dnnevna.png
