andraz213/UrbanNoiseSensing/Diplomska naloga/slike/Zbirna enota koncept delovanja (1)_popravljeno.jpg

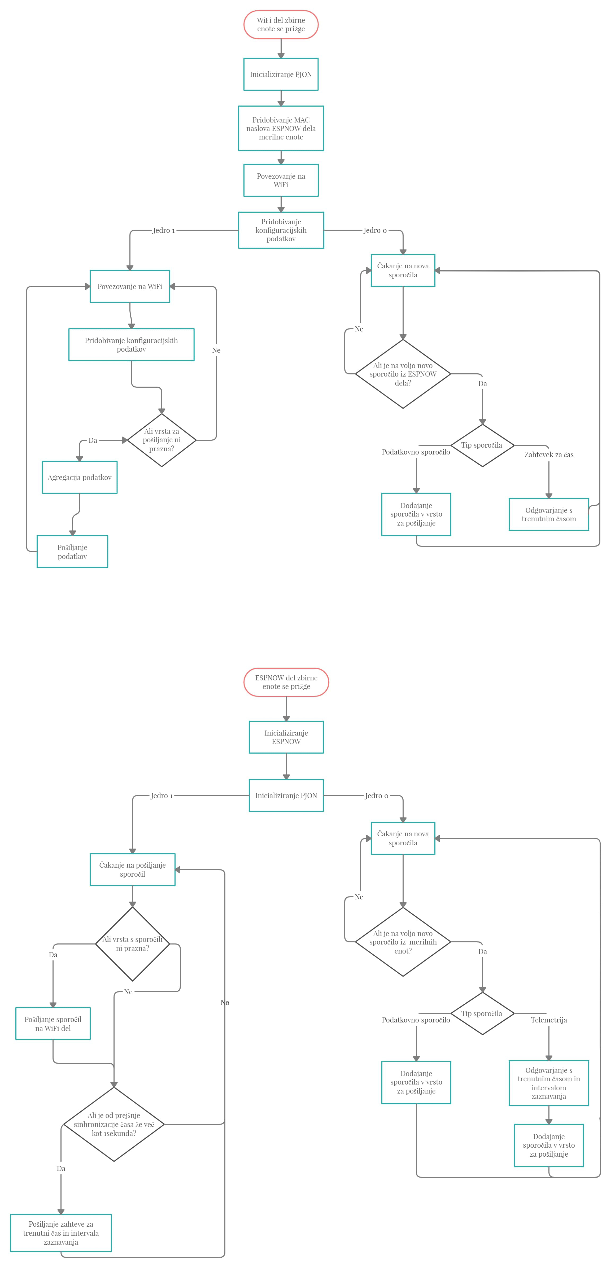
Diplomska naloga/slike/Zbirna enota koncept delovanja (1)_popravljeno.jpg
