andraz213/UrbanNoiseSensing/Diplomska naloga/slike/Zbirna enota koncept delovanja-2.jpg

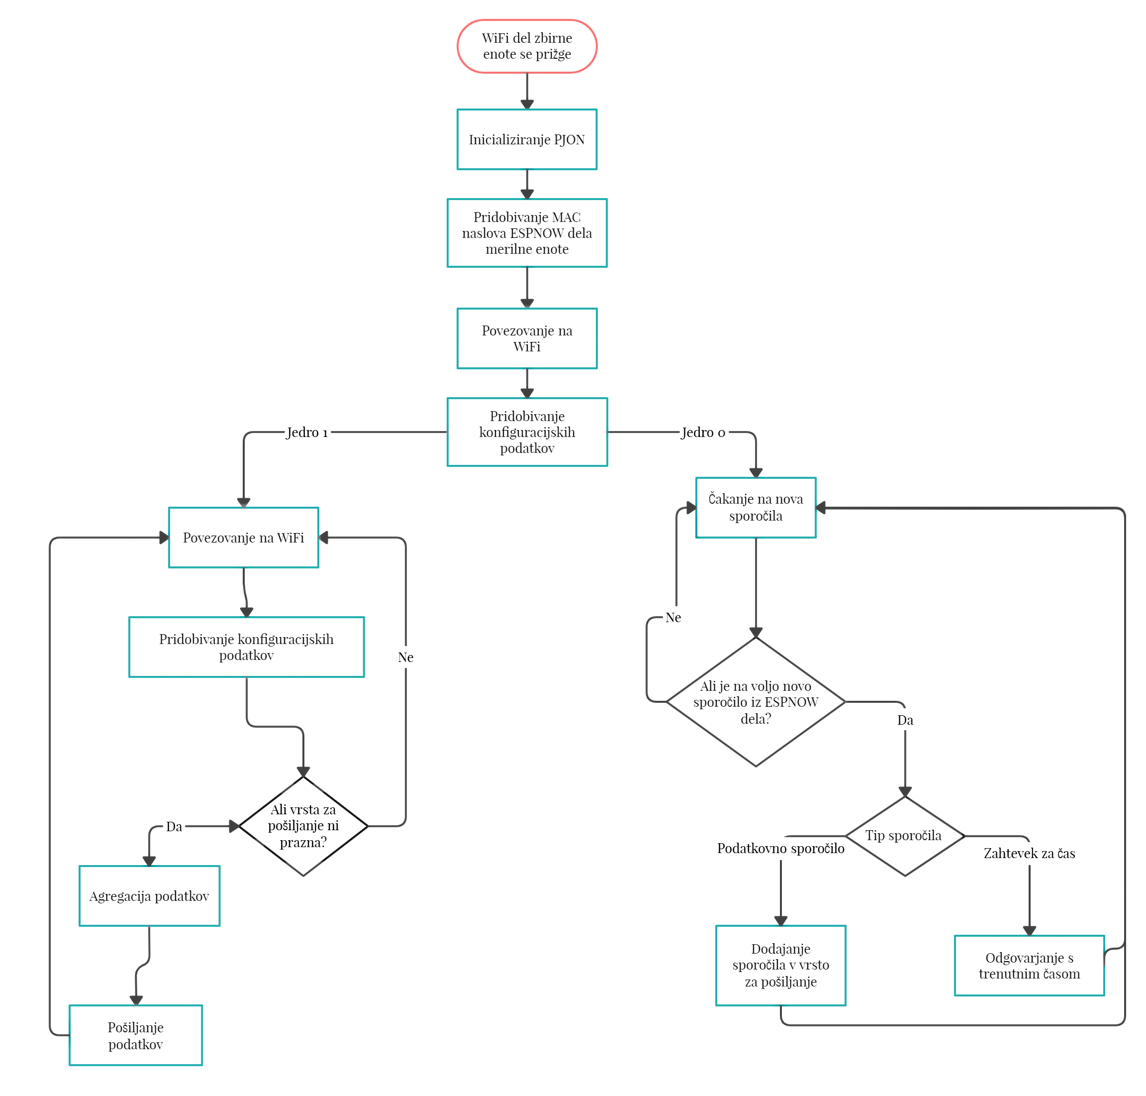
Diplomska naloga/slike/Zbirna enota koncept delovanja-2.jpg
