andraz213/UrbanNoiseSensing/Diplomska naloga/slike/Zbirna enota koncept delovanja.jpg

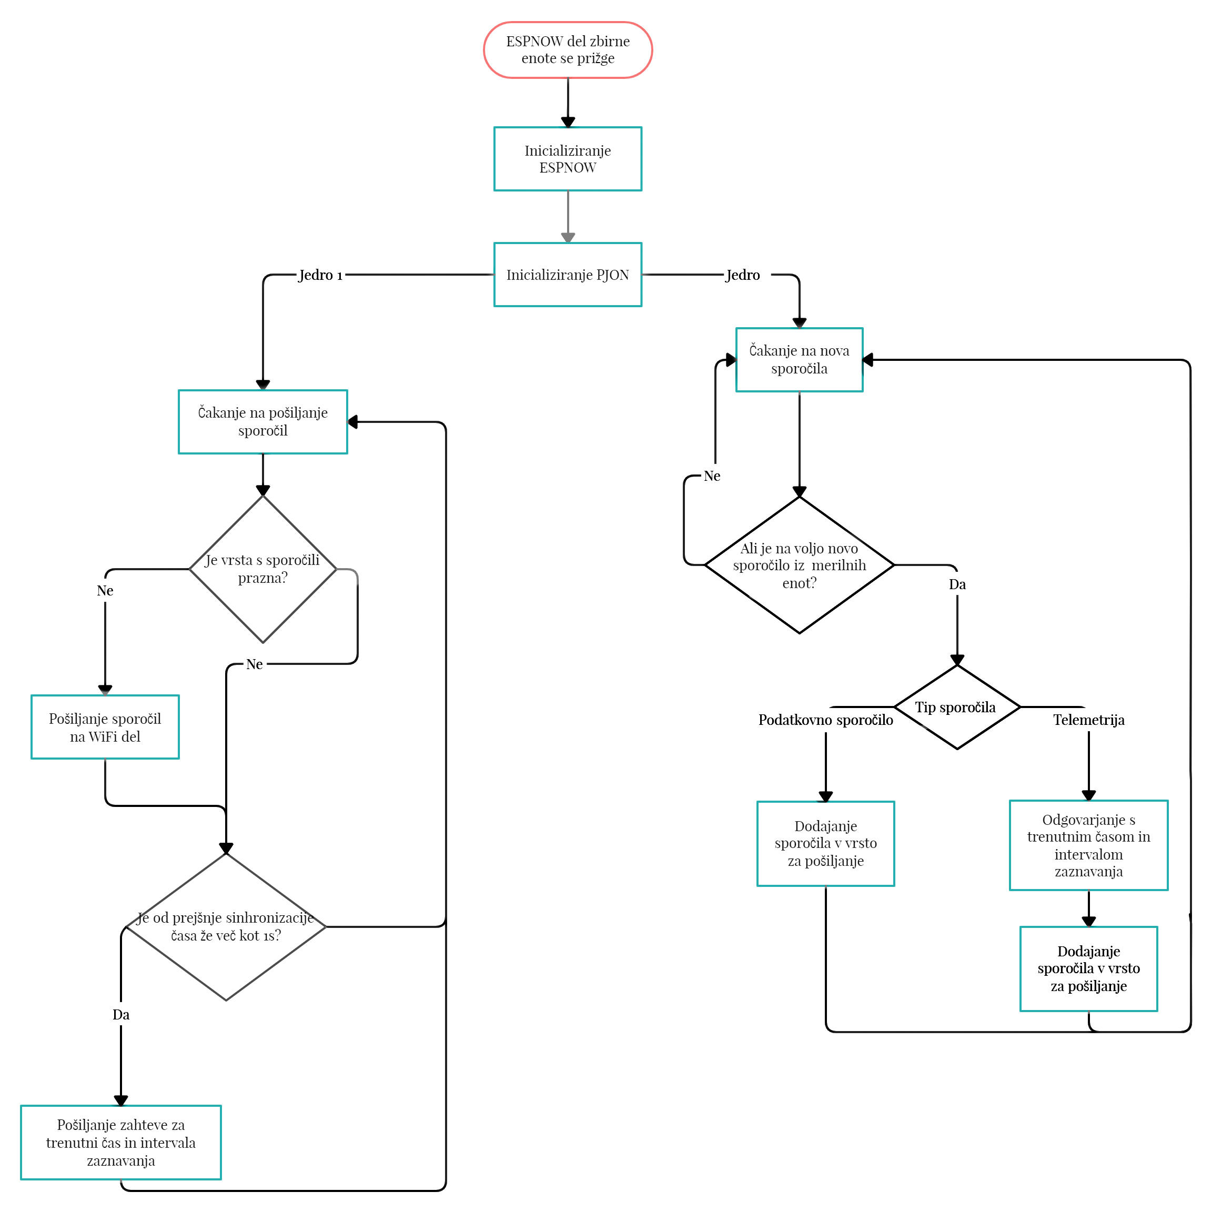
Diplomska naloga/slike/Zbirna enota koncept delovanja.jpg
