andraz213/UrbanNoiseSensing/Diplomska naloga/slike/Zbirna enota shematski prikaz.jpg

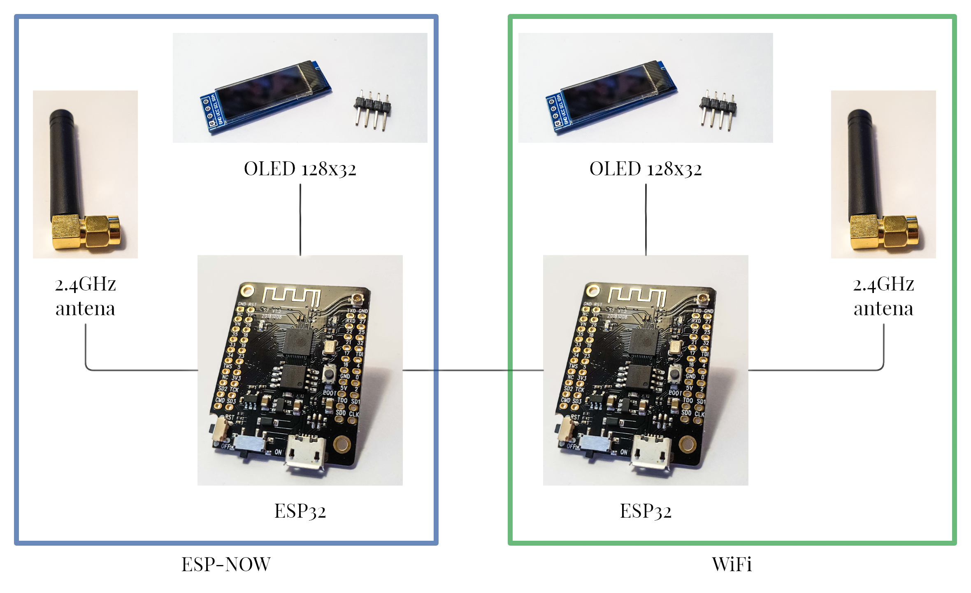
Diplomska naloga/slike/Zbirna enota shematski prikaz.jpg
