andraz213/UrbanNoiseSensing/Diplomska naloga/slike/zbirna_enota.png

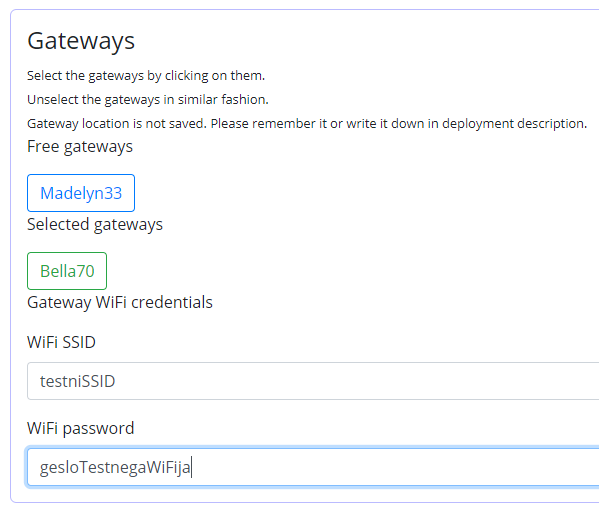
Diplomska naloga/slike/zbirna_enota.png
