andraz213/UrbanNoiseSensing/Diplomska naloga/slike/db_measurement.jpg

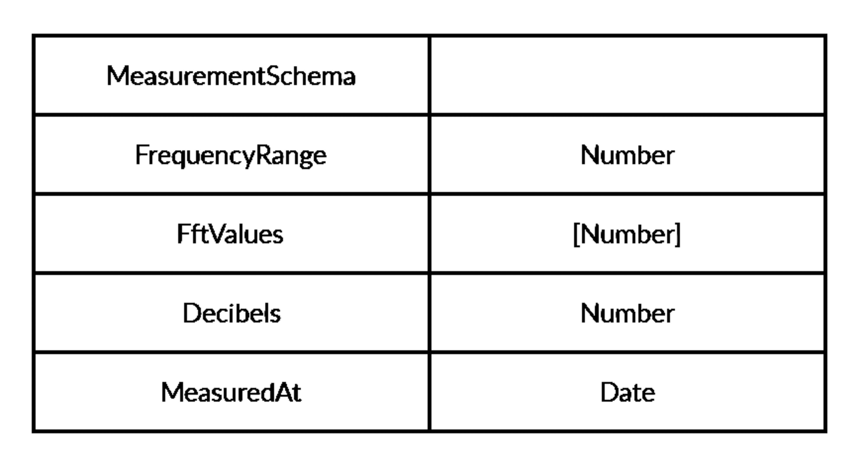
Diplomska naloga/slike/db_measurement.jpg
