andraz213/UrbanNoiseSensing/sensor firmware/gateway_espnow/handle_esp_now.h

#ifndef HANDLE_ESP_NOW_H
#define HANDLE_ESP_NOW_H


#include <Arduino.h>

void TaskEspNow( void *pvParameters );
void OnDataRecv(const uint8_t * mac, const uint8_t *incomingData, int len);
void init_wifi();
void handleTimeRequest(char* mac);
void handleSensorMessage(uint8_t * mac, uint8_t *incomingData, int len, int type);
void set_sensing_interval(int interval);
int get_meesages_last_mil(int mil);

#endif
