andraz213/UrbanNoiseSensing/sensor firmware/get_mic_data_and_send_fft/decibel_calculator.h

#ifndef DEC_CALC_H
#define DEC_CALC_H

#define LEQ_PERIOD        0.1           // second(s)
#define WEIGHTING         C_weighting // Also avaliable: 'C_weighting' or 'None' (Z_weighting)
#define LEQ_UNITS         "LAeq"      // customize based on above weighting used
#define DB_UNITS          "dBA"       // customize based on above weighting used
#define USE_DISPLAY       1

// NOTE: Some microphones require at least DC-Blocker filter
#define MIC_EQUALIZER     INMP441    // See below for defined IIR filters or set to 'None' to disable
#define MIC_OFFSET_DB     3.0103      // Default offset (sine-wave RMS vs. dBFS). Modify this value for linear calibration

// Customize these values from microphone datasheet
#define MIC_SENSITIVITY   -26         // dBFS value expected at MIC_REF_DB (Sensitivity value from datasheet)
#define MIC_REF_DB        94.0        // Value at which point sensitivity is specified in datasheet (dB)
#define MIC_OVERLOAD_DB   116.0       // dB - Acoustic overload point
#define MIC_NOISE_DB      29          // dB - Noise floor
#define MIC_BITS          24          // valid number of bits in I2S data
#define MIC_CONVERT(s)    (s >> 8)
#define MIC_TIMING_SHIFT  0           // Set to one to fix MSB timing for some microphones, i.e. SPH0645LM4H-x

// Calculate reference amplitude value at compile time








double calculate_decibels(int*input_samples, int num_samples);

#endif
