andraz213/UrbanNoiseSensing/Testiranje nrf24/NRF24_RECIEVE_EXAMPLE/NRF24_RECIEVE_EXAMPLE.ino

#include <SPI.h>
#include <nRF24L01.h>
#include <RF24.h>

//create an RF24 object
RF24 radio(9, 8);  // CE, CSN

//address through which two modules communicate.
const byte address[6] = "00001";

void setup()
{
  while (!Serial);
    Serial.begin(9600);
  
  radio.begin();
      radio.setPALevel(RF24_PA_MAX);           // If you want to save power use "RF24_PA_MIN" but keep in mind that reduces the module's range
  radio.setDataRate(RF24_250KBPS);
  
  //set the address
  radio.openReadingPipe(0, address);
  
  //Set module as receiver
  radio.startListening();
}

void loop()
{
  //Read the data if available in buffer
  if (radio.available())
  {
    char text[32] = {0};
    radio.read(&text, sizeof(text));
    Serial.println(text);
  }
}
